mcbronkowitch/fireflow/docs/hardware/captures/README.md

# Raw board captures — 2026-09-18/19 codec-tone campaign, 2026-09-28 pot round and scan check

Serial output from the Daisy Patch Submodule, as captured. Unedited.

These are here because committed files cite them **as the provenance of
numbers that ship**, and a citation pointing into deletable scratch is not a
citation:

| capture | what depends on it |
|---|---|
| `task-3-board-capture-1c15987.txt` | boot 1 of the four-boot boot-virgin floor |
| `task-4-board-capture-438fd51.txt` | boot 2 of the same |
| `task-4-board-capture-c5631f4.txt` | boot 3 of the same |
| `task-5-board-capture.txt` | boot 4, plus the whole window sweep |
| `task-6-board-capture-silent-arm.txt` | boot 5 — the silent-cadence arm, which answers section 6 |
| `pot-settle-capture-618427c.txt` | `shell/test_read_settle.py` (the real-block section) and the round-four write-up `docs/hardware/pots-measured.md` |
| `pot-wait-capture-e20b8fd.txt` | `shell/test_read_wait.py` (the real-block section) and the round-four write-up `docs/hardware/pots-measured.md` |
| `scan-check-capture-c04ba77.txt` | `shell/test_read_scan_check.py` (the capture section), the write-up `docs/hardware/scan-measured.md`, and `kPotHysteresis` in `shell/scan_value.h` |

The four-boot floor is `BOOT_VIRGIN_FLOOR` in `../../../shell/read_tone.py`,
which gate G8(b) compares against, and the same four columns appear in the
codec-tone design spec's section 7. Each figure is the `settled_mean_spread`
field of the `SHELL_TONE_STAT` lines at `case=-1` through `case=-5` — the
negative case numbers are the per-victim boot-virgin rows, emitted once per
boot before any `StartAudio()` and re-emitted verbatim every block.

`task-5-board-capture.txt` opens mid-block and closes mid-block; **lines 898
to 1852 are the one complete block**, and that block is also vendored as
`../../../shell/testdata/tone-block-86070d9.txt`, which the reader's guard
parses on every `ctest` run.

`task-6-board-capture-silent-arm.txt` is the run that answered
`../codec-tone-measured.md` section 6: the image `ab02aec+` carries the
silent-cadence arm (`level=3` on `SHELL_TONE_CASE`), so each block holds a
tone measurement and a no-tone measurement **at the same cadence**. It too
opens mid-block: **lines 1192 to 2401 are the one complete block**, and every
figure in that section comes from it. It carries **no `$$` overflow marker at
all** in 2925 lines, which is worth recording because the arm added 255 lines
to a block — those lines print slowly, one per phase point across a 10 ms
wait, so the extra volume never pressed on the host's drain rate. The reader's
guard parses this file on every `ctest` run as well.

This capture is one boot, three blocks. The two complete ones agree: across
their thirty tone-versus-silent rows no difference exceeds one count.

The round-one crosstalk capture of 2026-09-19 is **not** here: at 2 MB it is
an order of magnitude larger than these five, and its first complete block is
already committed in derived form as `../2026-09-19-xtalk.csv` and
`../2026-09-19-xtalk.csv.meta.csv`. Its `g6=0` readings across ten blocks are
recorded in `../crosstalk-measured.md` and exist in raw form only in the
session workspace.

`pot-settle-capture-618427c.txt` is the settle probe's pot-round image
(`SHELL_COUPON_PROBE=1 SHELL_SETTLE_PROBE=1 SHELL_POT_ROUND=1`), captured
2026-09-28 on the one coupon board with RV2, RV4 and RV6 set to mid travel. It
holds three complete blocks; the file opens mid-block, on a partial block
that started before the port opened, and the first complete block starts at
line 708.

`pot-wait-capture-e20b8fd.txt` is the wait probe's pot-round image
(`SHELL_COUPON_PROBE=1 SHELL_WAIT_PROBE=1 SHELL_POT_ROUND=1`), captured the
same day on the same board with the same pot settings. It too holds three
complete blocks after an opening partial one; the first complete block starts
at line 412.

`scan-check-capture-c04ba77.txt` is the panel scan's measurement image
(`SHELL_COUPON_PROBE=1 SHELL_SCAN_CHECK=1`), captured 2026-09-28 on the same
board, RV2, RV4 and RV6 still at mid travel from the pot round, the engine
playing and the codec running. It holds five complete run blocks; lines 1–75
are a partial opening (line 2 carries a `$$` marker), and the first complete
block starts at line 76. The guard also compares `kPotHysteresis` with the H
it computes from this file, so replacing the capture moves the constant.

A capture is evidence, not a document. Nothing here is edited to read better,
and where a capture contradicts a write-up, the capture wins.
