mcbronkowitch/fireflow/docs/hardware/io-budget.md

# I/O-Budget — FireFlow auf 60 HP

> **Stand 2026-08-30.** Ursprünglich am 2026-08-08 (Git `9326fee`) als
> **Vorarbeit auf 42 HP** geschrieben, mit leerer Einstufungsspalte in §2, weil
> die Panel-Reduktion Instrumentendesign ist und Bastian gehört.
>
> **Diese Prämisse ist zweimal überholt worden, und beide Male nach oben.** Die
> Envelope-Entscheidung (`2026-08-08-fireflow-hardware-envelope-design.md`)
> setzte 60 HP mit vollem Control-Set, und die Bedienelement-Reduktion
> (`2026-08-09-hw-control-reduction-design.md`) senkte das Inventar von 82 auf
> 68 Parameter. Danach haben **drei Panel-Runden** — Neugruppierung (2.21.1),
> Neuverteilung (2.21.2) und Plattenrunde 2a (2.21.3) — Controls verschoben,
> zusammengelegt und die Bauform geändert.
>
> **Nachtrag 2026-08-19.** Zwei Zahlen korrigiert, beide gefunden, indem der
> Generator gelaufen ist statt zitiert zu werden — der Fehler, vor dem §1
> warnt: die 595-Bilanz rechnete mit den **21** LEDs des Rack-Panels statt den
> **19** der Hardwareplatte (§3, §4), und die CPU-Reserve stand als
> Seed-Hochrechnung (2,17 Punkte) statt als die inzwischen direkt gemessenen
> ~2,9 (§6). Beide Korrekturen gehen zugunsten des Entwurfs aus.
>
> **Nachtrag 2026-08-30. §1, §2 und §4 neu gemessen, und es hatte sich wieder
> bewegt.**
> Zwischen dem 19. und dem 30. August sind die MOD-Latch-Runde
> (`2026-08-22-mod-latch-layer-design.md`) und PAN (`2026-08-30-pan`) gelandet;
> §1 stand danach elf Tage falsch da. Es waren keine Rundungsfehler, sondern das
> Inventar: 69 → **75** Parameter auf der Platte, 67 → **73** Positionen, die
> Bauformverteilung 16/51/2 → **14/58/3**, `HW_ONLY` 2 → **1** (`MODBTN` ist ein
> echter `ParamId` geworden), und die Kernaussage „keine hardware-only
> Parameter" musste ihre Prüfmenge wechseln (`PARAMS`, nicht
> `RUNTIME_PANEL_PARAMS`). Der Grund, dass es niemandem auffiel: der Wächter
> `tools/test_count_panel_controls.py` stand seit dem 7. August rot und wurde
> gelesen wie Rauschen. Er ist am 2026-08-30 neu geeicht, mit der Anweisung, §1
> im selben Commit mitzuziehen.
>
> **§2 und §4 sind am selben Tag mitgezogen worden.** §2 trug eine
> 69-Zeilen-Tabelle; die Platte hat 75. Sie ist neu **erzeugt** statt
> nachgepflegt — und dabei kam heraus, dass nicht nur sechs Zeilen fehlten:
> **25 der alten 69 hatten auch ihre Position oder ihre Bauform geändert**
> (`REV_MIX_A/B` ist gar kein grosser Poti mehr). §4 nannte „67
> Poti-/Taster-Positionen, 2 reservierte Pads"; es sind **73** und **1**, und
> die Geometriezeile hatte eine Reihe (76 → 74,4) und beide waagerechten Ränder
> falsch. Die 19 LEDs, 18 Buchsen und der SD-Slot stimmten durchweg.
>
> **Was das für dieses Dokument heißt:** §1, §2 und §4 sind auf das **gebaute**
> Panel nachgezogen und am 2026-08-30 gemessen. §5 (Buchsen, 12/6) gilt
> unverändert weiter, am selben Tag gegengeprüft. §3 (Pins) ist von der
> Parameterzahl unabhängig und steht unverändert; es hat nur einen Nachtrag zur
> Mux-Topologie bekommen. §6 listet, was heute noch offen ist — es ist eine
> andere Liste als 2026-08-08.
>
> **Stand 2026-10-08: welche Teile noch die Platte vor dem 9-mm-Raster
> beschreiben.** Die 9-mm-Korrektur (Spec `2026-10-07-panel-nine-mm-raster-design.md`)
> hat jedes Bedienelement neu gesetzt. Gemessen am 2026-10-09:
> `python res/gen_hw_panel.py` druckt `params=75 inputs=12 outputs=6 lights=15
> panel=60HP`. Die folgenden Stellen sind **nicht** nachgezogen; sie stehen auf
> dem Stand 2026-08-30 und werden mit diesen Zahlen gelesen:
>
> - **§1, Codeblock (`lights=19`):** heute `lights=15`. Die Bauformtabelle zählt
>   Parameter-Positionen nach `HW_PARAMS` (14 / 56 / 3); mit `HW_ONLY` sind es
>   **77 Positionen**: 14 grosse Potis, 59 kleine (darunter drei reservierte), 4
>   Taster. Das sind 73 Potis und 4 Taster.
> - **§1, „1 Element … `HW_ONLY`“:** heute **4**: `SHIFTBTN` (Taster) und die
>   drei reservierten Potis `ROOT_A`, `ROOT_B`, `REV_MOD` (Beschriftung ROOT
>   und WOBL), die einen Mux-Kanal lesen, aber nichts schicken. Die Zahl der
>   Taster bleibt 4.
> - **§1, Körperradien „6,0 / 4,4 / 4,0 mm“:** heute `BODY_R` = **6,0 / 3,85 /
>   3,0 mm** (gross / klein / Taster); `CLASS_R` ist unverändert 8,5 / 6,0 /
>   4,0 mm.
> - **§3, 595-Zeile (19 LEDs, 5 Enables):** heute 15 LEDs, und die Kette ist
>   40 Bit lang: Adresse Bit 0–2, Enables Bit 3–12 (zehn, eins je Mux), LEDs
>   Bit 13–27 (`shell/generated_panel_map.h`). Die Mux-Zeile steht im Nachtrag
>   2026-10-08 in §3.
> - **§4, „neun Linien“, y = 114 mm, 19 LEDs, 1 reserviertes Pad:** heute
>   **fünf Reihen** bei y = 14,5 / 34,625 / 54,75 / 74,875 / 95,0 mm (Raster
>   20,125 mm), die Buchsenreihe bei **y = 112,75 mm** (`JACK_Y`), die
>   Bedienelemente von x = 11,0 bis x = 293,8 mm, **15 LEDs**, und
>   `SHIFTBTN` ist das eine reservierte Pad (daneben die drei reservierten
>   Potis). Plattenmaß 304,8 × 128,5 mm unverändert.

## 1. Die Ausgangslage

**Autorität ist der Generator, nicht dieses Dokument.** Eine Handzählung
veraltet beim nächsten Panel-Commit; jede Zahl unten stammt aus einem Lauf und
ist mit ihm reproduzierbar.

```
python host/vcv/res/gen_hw_panel.py          # aus host/vcv/, idempotent
params=75 inputs=12 outputs=6 lights=19  panel=60HP

python tools/count_panel_controls.py         # aus dem Repo-Wurzelverzeichnis
panel 68 · appended 6 · runtime 74 · part_a 20 · part_b 20 · shared 10
```

Beide Zahlen sind gemessen 2026-08-30. **Sie sind nicht mehr dieselbe Zahl, und
das ist kein Fehler:** die Platte trägt 75 Parameter, `RUNTIME_PANEL_PARAMS`
hat 74. Der eine Unterschied ist `MODBTN`. Er ist trotzdem **kein**
hardware-only *Parameter* — er ist ein echter `ParamId`, er kommt nur aus einem
anderen Block: `MOD_LAYER_PARAMS` (51 ids, Spec
`2026-08-22-mod-latch-layer-design.md`), nicht aus der Panel-Liste. Zusammen
sind das `gen_panel.PARAMS` = 74 + 51 = **125**, und *gegen die* ist die
Differenzmenge leer: kein Element der Hardwareplatte ist ein Parameter, den
VCV nicht auch hat.

> **Die alte Formulierung prüfte gegen `RUNTIME_PANEL_PARAMS` und stimmt seit
> der MOD-Latch-Runde nicht mehr.** Wer die Aussage nachprüft, muss gegen
> `gen_panel.PARAMS` prüfen, sonst fällt `MODBTN` fälschlich als
> hardware-only heraus.

Was auf der Hardware existiert und **gar keinen** Parameterwert hat, sind die
LEDs und ein einziger Taster — siehe unten.

**75 Parameter auf 73 physischen Positionen.** Die Differenz sind die beiden
bewussten Doppelbelegungen: `STAGES_A/B` (BEND) teilt sich den Knopf mit
`ATTACK_A/B` (68,25 / 34,00 und 236,55 / 34,00), mit engine-abhängigem
Moduswechsel. Das ist die einzige Mehrfachbelegung auf dem Panel.

Nach Bauform **auf der Hardware** — nicht nach dem VCV-Glyph, der eine andere
Größenklasse haben darf und bei mehreren Controls auch hat:

| Bauform | Radius | Anzahl | Positionen |
|---|---:|---:|---:|
| grosser Poti (`G`) | 8,5 mm | 14 | 14 |
| kleiner Poti (`S`) | 6,0 mm | 58 | 56 |
| Taster (`P`) | 4,0 mm | 3 | 3 |
| **Summe** | | **75** | **73** |

Die Radiusspalte ist `CLASS_R` — der Abstandsradius, mit dem das Layout rechnet,
nicht der Körper. Die Körperradien (`BODY_R`) sind 6,0 / 4,4 / 4,0 mm.

Dazu **1** Element, das gar keinen `ParamId` hat und deshalb in keiner der
Zahlen oben steckt (`HW_ONLY` im Generator):

| Element | Art | Anmerkung |
|---|---|---|
| `SHIFTBTN` | Taster | reserviert, ohne Funktion — 1 weiteres Pad |

Macht **4 Taster**: `REC_A/B`, `MODBTN` (seit der MOD-Latch-Runde ein echter
Parameter, kein `HW_ONLY` mehr — deshalb steht er jetzt in der `P`-Zeile oben)
und das reservierte `SHIFTBTN`.

**Die LEDs laufen seit der LED-Feedback-Runde (2026-08-16) nicht mehr über
`HW_ONLY`.** Alle Lampen auf der Platte sind jetzt echte `LightId`s.

> **Drei verschiedene LED-Zahlen, und dieser Abschnitt hat sie bis 2026-08-19
> vermischt.** Sie sind alle drei richtig, nur für verschiedene Dinge:
>
> | Zahl | Was sie zählt | Woher |
> |---:|---|---|
> | **17** | `LightId`s insgesamt, alle jeden Block geschrieben | `gen_panel.LIGHTS` (4) + `HW_ONLY_LIGHTS` (13) |
> | **15** | Lampen auf der **Hardwareplatte** | `gen_hw_panel.py` druckt `lights=15` |
> | **4** | Lampen auf dem **Rack**-Panel | `count_panel_controls.py` druckt `lights 4` |
>
> Die 15 sind die 17 ohne `FLOW_A_L`/`FLOW_B_L`, die `_SKIP_HW_LIGHTS` auf der
> Hardwareplatte bewusst weglässt. **Für die 595-Kette zählen die 15** — sie
> trägt physische Lampen, keine `LightId`s (§3). *Stand 2026-10-08: die
> 9-mm-Korrektur (Spec 2026-10-07 §5) hat die Platte von 19 auf 15 Lampen
> gebracht; die Zahlen 21 und 19 stammten aus der Zeit davor.*

Der Bestand: 8 der bisherigen 10 blieben, `CAP_A_L`/`CAP_B_L` sind mit der
Capture-Sequenz gelöscht (die gibt es seit 2026-07-14 nicht mehr, siehe
`docs/roadmap.md`), und 13 sind neu *(Stand 2026-08-19; 8 + 13 sind 21, die Zahl
des Rack-Panels jener Zeit, nicht die 17 `LightId`s und 15 Plattenlampen des
Kastens oben)*. *(Stand 2026-10-08, 15 Lampen auf der
Platte, Spec 2026-10-07 §5: `SYNC_L` heißt jetzt `CLK_L` und soll jeden Impuls
an der CLOCK-Buchse blitzen; neu sind `RST_L`, `FTIME_A_L`/`FTIME_B_L`. Die
zwei Pad-Lampen `SHIFTBTN_L` und `MODBTN_L` stehen zwischen ihrer Taste und
ihrer Buchse und **tragen je zwei Aufgaben**: `SHIFTBTN_L` zeigt gerastetes
SHIFT, sonst den Eingangspegel; `MODBTN_L` zeigt MODs Doppelpuls, sonst den
Master-Limiter, den vorher `CEIL_L` zeigte, das damit entfällt.)* Von diesen
ist heute im Code nur `MODBTN_L` belegt; `CLK_L`, `RST_L`, `FTIME_*_L` und `SHIFTBTN_L`
sind vorerst dunkel — ihre Bedeutung ist P6b (`led_law.hpp`, `fill()`) —, aber
jeden Block *geschrieben*, nicht übersprungen; ein Gate prüft das. Das
gilt auch für `FLOW_A_L`/`FLOW_B_L`, die geschrieben werden, obwohl die
Hardwareplatte sie nicht zeichnet. `TEMPO_L` tickt den Transport-Beat
(Metronom-Puls, `kTempoPulse` der Beat-Phase). Herleitung, Platzierung und die offene
Mux-Breite (8:1 gegen 16:1, deshalb nimmt `duty()` den Schrittzähler als
Parameter): Spec
[`2026-08-16-led-feedback-design.md`](../superpowers/specs/2026-08-16-led-feedback-design.md)
§2–§3, und `docs/roadmap.md`.

> **Die LED-Zahl war erst gefallen, und zwar absichtlich.** Die Neugruppierung
> hatte das Feld auf 20 festgelegt (Envelope-Spec §1, oberes Ende des
> Korridors); die Neuverteilung hat `ENGINE_A/B` vom Taster zum
> **fünf-Zonen-Rastpoti** am Kopf der VOICE-Gruppe gemacht und damit zehn
> Anzeige-LEDs eingespart. 20 − 10 = 10, und die Kette blieb dieselbe — bis
> die LED-Feedback-Runde das Feld auf 21 `LightId`s anhob (19 davon auf der
> Platte, siehe Kasten oben), mehr als das ursprüngliche Korridor-Ende, weil
> kein Rundungsdruck mehr bestand.

`HIDDEN_PARAMS` ist seit der Reduktionsrunde leer — es gibt keinen menü-only
*Parameter* mehr. Das Kontextmenü selbst existiert weiter (Resync to bar, BBD
Freeze Attack, die Sampler-Untermenüs, Excitation-Flags), es trägt nur keinen
Wert mehr, der nicht auch auf dem Panel sitzt.

## 2. Die 75 Parameter

Die Einstufungsspalte dieses Abschnitts war bis 2026-08-09 leer und war die
offene Frage des ganzen Dokuments. **Sie ist entschieden.** Was hier steht, ist
nicht mehr eine Absicht, sondern das gebaute Panel, ausgelesen aus
`host/vcv/res/gen_hw_panel.py` (`HW_PARAMS`, `hw_class()`, Positionen in mm vom
linken oberen Panelrand). Die Prüfsumme der Zeilen ist **75**.

**Die Tabelle ist generiert, nicht gepflegt** (Neustand 2026-08-30). Reihenfolge
und Nummerierung sind die von `HW_PARAMS`, die Bauform kommt aus `hw_class()`,
die Gruppe aus `PART_A`/`PART_B`/`SHARED` — alles andere bekommt „—". Wer sie
neu erzeugt, prüft die Herleitung daran, dass die unveränderten Zeilen Zeichen
für Zeichen zurückkommen.

> **Sie stand länger falsch da, als die sechs fehlenden Zeilen vermuten
> lassen.** Beim Neuerzeugen kamen nicht nur die neuen Parameter dazu: **25 der
> alten 69 Zeilen hatten sich bewegt** (gemessen, nicht geschätzt — die
> übrigen 44 kamen unverändert zurück). `ENGINE_A/B` sitzt jetzt in der oberen
> Außenecke (16,25 bzw. 288,55 / 14,50) statt bei y = 50,22. **Die Reihe
> y = 76 gibt es nicht mehr:** sie ist auf 74,4 (TUNE, DETUNE, REV_SIZE,
> REV_DIFF) und 79 (FLUX, COMP) aufgeteilt. Von y = 95 sind einzelne Elemente
> auf 97 gerückt (GRIT, FLUXFB, REV_MIX) — die Reihe 95 selbst gibt es weiter,
> `COLOR_A/B` steht unverändert darauf. `SOURCE_A/B` und `FILT_A/B` sind
> waagerecht gerückt, und `REV_MIX_A/B` ist vom **grossen** auf den **kleinen**
> Poti gewechselt. Welche der Runden das jeweils war, steht hier bewusst nicht
> — es wurde nicht nachgeschlagen. Eine Position aus der alten Tabelle zu
> zitieren, hätte ein Bohrbild ruiniert.

| # | Parameter | Bauform auf der Hardware | Gruppe | Position (mm) |
|---:|---|---|---|---|
| 1 | `RATE_A` | kleiner Poti | PART_A | 61,00 / 14,50 |
| 2 | `SHAPE_A` | kleiner Poti | PART_A | 18,25 / 34,00 |
| 3 | `DENSITY_A` | grosser Poti | PART_A | 40,75 / 53,00 |
| 4 | `SMOOTH_A` | kleiner Poti | PART_A | 31,25 / 34,00 |
| 5 | `RANGE_A` | kleiner Poti | PART_A | 44,25 / 34,00 |
| 6 | `MELODY_A` | kleiner Poti | PART_A | 74,00 / 14,50 |
| 7 | `MOD_A` | grosser Poti | PART_A | 21,75 / 53,00 |
| 8 | `TUNE_A` | kleiner Poti | PART_A | 17,00 / 74,40 |
| 9 | `ATTACK_A` | kleiner Poti | PART_A | 68,25 / 34,00 — geteilt mit `STAGES_A` |
| 10 | `DECAY_A` | kleiner Poti | PART_A | 81,25 / 34,00 |
| 11 | `RES_A` | kleiner Poti | PART_A | 94,25 / 34,00 |
| 12 | `SUB_A` | kleiner Poti | PART_A | 107,25 / 34,00 |
| 13 | `SOURCE_A` | kleiner Poti | PART_A | 72,88 / 50,22 |
| 14 | `FLUX_A` | grosser Poti | PART_A | 67,00 / 79,00 |
| 15 | `GRIT_A` | kleiner Poti | PART_A | 116,75 / 97,00 |
| 16 | `COMP_A` | grosser Poti | PART_A | 106,50 / 79,00 |
| 17 | `STEPS_A` | kleiner Poti | PART_A | 35,00 / 14,50 |
| 18 | `ENGINE_A` | kleiner Poti | PART_A | 16,25 / 14,50 |
| 19 | `DETUNE_A` | kleiner Poti | PART_A | 30,00 / 74,40 |
| 20 | `SONG_A` | kleiner Poti | PART_A | 48,00 / 14,50 |
| 21 | `RATE_B` | kleiner Poti | PART_B | 243,80 / 14,50 |
| 22 | `SHAPE_B` | kleiner Poti | PART_B | 286,55 / 34,00 |
| 23 | `DENSITY_B` | grosser Poti | PART_B | 264,05 / 53,00 |
| 24 | `SMOOTH_B` | kleiner Poti | PART_B | 273,55 / 34,00 |
| 25 | `RANGE_B` | kleiner Poti | PART_B | 260,55 / 34,00 |
| 26 | `MELODY_B` | kleiner Poti | PART_B | 230,80 / 14,50 |
| 27 | `MOD_B` | grosser Poti | PART_B | 283,05 / 53,00 |
| 28 | `TUNE_B` | kleiner Poti | PART_B | 287,80 / 74,40 |
| 29 | `ATTACK_B` | kleiner Poti | PART_B | 236,55 / 34,00 — geteilt mit `STAGES_B` |
| 30 | `DECAY_B` | kleiner Poti | PART_B | 223,55 / 34,00 |
| 31 | `RES_B` | kleiner Poti | PART_B | 210,55 / 34,00 |
| 32 | `SUB_B` | kleiner Poti | PART_B | 197,55 / 34,00 |
| 33 | `SOURCE_B` | kleiner Poti | PART_B | 231,93 / 50,22 |
| 34 | `FLUX_B` | grosser Poti | PART_B | 237,80 / 79,00 |
| 35 | `GRIT_B` | kleiner Poti | PART_B | 188,05 / 97,00 |
| 36 | `COMP_B` | grosser Poti | PART_B | 198,30 / 79,00 |
| 37 | `STEPS_B` | kleiner Poti | PART_B | 269,80 / 14,50 |
| 38 | `ENGINE_B` | kleiner Poti | PART_B | 288,55 / 14,50 |
| 39 | `DETUNE_B` | kleiner Poti | PART_B | 274,80 / 74,40 |
| 40 | `SONG_B` | kleiner Poti | PART_B | 256,80 / 14,50 |
| 41 | `MORPH` | grosser Poti | SHARED | 152,40 / 53,00 |
| 42 | `TEMPO` | kleiner Poti | SHARED | 139,40 / 34,00 |
| 43 | `COUPLE` | kleiner Poti | SHARED | 152,40 / 34,00 |
| 44 | `SCALE` | kleiner Poti | SHARED | 132,90 / 14,50 |
| 45 | `DRIFT` | kleiner Poti | SHARED | 145,90 / 14,50 |
| 46 | `REV_SIZE` | kleiner Poti | SHARED | 136,40 / 74,40 |
| 47 | `REV_DECAY` | grosser Poti | SHARED | 152,40 / 79,00 |
| 48 | `REV_TONE` | kleiner Poti | SHARED | 152,40 / 97,00 |
| 49 | `REV_DIFF` | kleiner Poti | SHARED | 168,40 / 74,40 |
| 50 | `CHOKE` | kleiner Poti | SHARED | 158,90 / 14,50 |
| 51 | `FILT_A` | grosser Poti | — | 88,88 / 53,00 |
| 52 | `FILT_B` | grosser Poti | — | 215,93 / 53,00 |
| 53 | `TIDE` | kleiner Poti | — | 136,40 / 50,22 |
| 54 | `FLUXRATE_A` | kleiner Poti | — | 54,00 / 89,86 |
| 55 | `FLUXRATE_B` | kleiner Poti | — | 250,80 / 89,86 |
| 56 | `FLUXFB_A` | kleiner Poti | — | 67,00 / 97,00 |
| 57 | `FLUXFB_B` | kleiner Poti | — | 237,80 / 97,00 |
| 58 | `COLOR_A` | grosser Poti | — | 23,50 / 95,00 |
| 59 | `COLOR_B` | grosser Poti | — | 281,30 / 95,00 |
| 60 | `LINK_A` | kleiner Poti | — | 80,00 / 89,86 |
| 61 | `LINK_B` | kleiner Poti | — | 224,80 / 89,86 |
| 62 | `STAGES_A` | kleiner Poti | — | 68,25 / 34,00 — geteilt mit `ATTACK_A` |
| 63 | `STAGES_B` | kleiner Poti | — | 236,55 / 34,00 — geteilt mit `ATTACK_B` |
| 64 | `REC_A` | Taster | — | 101,00 / 14,50 |
| 65 | `REC_B` | Taster | — | 203,80 / 14,50 |
| 66 | `REV_MIX_A` | kleiner Poti | — | 129,75 / 97,00 |
| 67 | `REV_MIX_B` | kleiner Poti | — | 175,05 / 97,00 |
| 68 | `SHUFFLE` | kleiner Poti | — | 165,40 / 34,00 |
| 69 | `PACE` | kleiner Poti | — | 168,40 / 50,22 |
| 70 | `DEPTH_A` | kleiner Poti | — | 104,88 / 50,22 |
| 71 | `DEPTH_B` | kleiner Poti | — | 199,93 / 50,22 |
| 72 | `PULL` | kleiner Poti | — | 171,90 / 14,50 |
| 73 | `PAN_A` | kleiner Poti | — | 103,75 / 97,00 |
| 74 | `PAN_B` | kleiner Poti | — | 201,05 / 97,00 |
| 75 | `MODBTN` | Taster | — | 290,80 / 114,00 |

**Zugegangen seit der Reduktion** — sechs Zeilen, und keine davon hat etwas
verdrängt. Das ist der eigentliche Beleg dafür, dass „one in, one out" tot ist:

| Zeile | Parameter | Woher |
|---:|---|---|
| 69 | `PACE` | globaler Modulations-Zeitdehner, Spec 2026-08-12 modulation-pace |
| 70–71 | `DEPTH_A/B` (DPTH) | die `LANE_MOTION`-Basis, aus FEED gewachsen — Spec 2026-08-18 feed §4, auf alle sechs Engines gezogen in 2026-08-19 voice-knobs-dpth-edge |
| 72 | `PULL` | bipolare Akkord-Schwerkraft zwischen den Decks, Spec 2026-07-19 pull-chord-gravity |
| 73–74 | `PAN_A/B` | Deck-Balance im Master-Mix, Spec 2026-08-30 pan — auf `LEVEL_SLOTS[0]`, den die Platte dafür freigehalten hatte |
| 75 | `MODBTN` | **kein neues Bedienelement.** Das Pad gab es schon, es lief bis zur MOD-Latch-Runde (Spec 2026-08-22) als `HW_ONLY` ohne Parameterwert — jetzt ist es ein echter `ParamId` und zählt mit (§1) |

**Der Satz, der hier bis 2026-08-30 stand** — `PACE` sei „der einzige
Parameter, den das Instrument seit der Reduktion dazubekommen hat" — wurde mit
`d18e50f` (2026-08-19, DPTH) falsch und ist es elf Tage lang geblieben;
`ee23912` (08-22, PULL) und `32835ff` (08-30, PAN) sind danach darüber
hinweggelaufen.

**Retiriert und nicht mehr Teil der Zählung** (Begründung in
`2026-08-09-hw-control-reduction-design.md`): `GRITMODE_A/B`, `STEP_A/B`,
`FORM_A/B`, `NEWPHRASE_A/B`; `SYNC`, `SPOT`, `MASTER_DRIVE`, `SETTLE`,
`REV_SMEAR`, `REV_MOD`; `FLUXTIME_A/B` (in FLUX aufgegangen); `DRIVE_A/B`
(ersatzlos, BBD-Drive kommt aus `bbd_engine.cpp`).

**Dazugekommen und wieder weg, ohne je in dieser Tabelle gestanden zu haben:**
`DAMP_A/B` (der EDGE-Knopf, ROW_V2 unter DPTH) kam am 2026-08-19 mit DPTH und
ging am 2026-08-20 wieder (Plan `edge-knob-removal`) — gemessen und verworfen,
er hat seinen Panelplatz nicht verdient. Der Platz bleibt absichtlich leer;
freigewordene Slots werden nicht neu gruppiert.

**Eine offene Kleinigkeit, die genau hier auffällt:** `STAGES` hat im Generator
ein **leeres Plattenwort** (`HW_CAPTION["STAGES"] = ""`), BEND wird also gar
nicht aufs Panel gedruckt. Das ist bekannt und nicht entschieden — auf der
Hardware ist der Knopf da, die Beschriftung nicht.

## 3. Was das Patch Submodule wirklich hergibt

Gelesen aus `lib/libDaisy/src/daisy_patch_sm.h` (Pinliste) und
`daisy_patch_sm.cpp:10-21` (ADC-Zuordnung). **Das ist der Teil dieses
Dokuments, der die Reduktion am härtesten einschränkt** — und der einzige, den
die drei Panel-Runden nicht berührt haben.

Das Modul hat 40 Anschlüsse (A1–A10, B1–B10, C1–C10, D1–D10). Davon sind
vergeben und nicht verfügbar:

| Pins | Belegung |
|---|---|
| A1, A4, A5, A6, A7, A10 | −12 V, GND, +12 V, +5 V, GND, +3V3 |
| A8, A9 | USB D−/D+ — **wird für DFU gebraucht**, das Board hat keine SWD-Pins |
| B1–B4 | Audio Out R/L, Audio In R/L |

Bleibt für Bedienelemente und Buchsen:

| Pins | Funktion | brauchbar als |
|---|---|---|
| C2–C9 | CV In 1–8 | 8 ADC-Eingänge **mit bipolarer Eingangsstufe** (±5 V → 0–3,3 V) |
| **A2, A3** | UART1 Rx/Tx | **ADC 9/10 — rohe 0–3,3-V-Eingänge** |
| **D8, D9** | SPI2 MISO/MOSI | **ADC 11/12 — rohe 0–3,3-V-Eingänge** |
| C1, C10 | CV Out 1/2 | 2 DAC-Ausgänge, **0–5 V unipolar** |
| B5, B6 | Gate Out 1/2 | 2 digitale Ausgänge |
| B9, B10 | Gate In 1/2 | 2 digitale Eingänge |
| B7, B8 | I2C1 SCL/SDA | I2C oder 2 GPIO |
| D1, D10 | SPI2 CS/SCK | SPI oder 2 GPIO |
| D2–D7 | SDMMC | SD-Karte oder 6 GPIO |

### Die entscheidende Zahl: vier rohe ADC-Pins

Ein Poti liefert 0–3,3 V. Dafür taugen **A2, A3, D8, D9** — die acht CV-Pins
tragen die bipolare Eingangsstufe des Moduls und würden ein unipolares
Potisignal auf einen Teil des ADC-Bereichs stauchen.

> **Nachtrag 2026-08-08 (Envelope-Spec §2), und er ändert das Ergebnis:** die
> Rechnung unten geht davon aus, dass die Adressleitungen GPIOs kosten. Das tun
> sie nicht mehr — **Adress- *und* Enable-Leitungen der 74HC4067 wandern auf die
> 595-Kette.** Damit teilen sich bis zu **acht** Muxe die vier Sense-Pins:
> **128 Kanäle für null GPIOs.** Genau diese Einsparung ist es, die den
> 4-bit-SD-Anschluss überhaupt möglich macht. Bedarf heute: **67 Positionen** —
> die Mux-Kapazität ist damit nicht mehr die knappe Ressource, die sie 2026-08-08
> war.

```
Mux-Kanäle = rohe ADC-Pins × Kanäle pro Chip

  4 × 74HC4051  (8:1)  = 32 Kanäle,  3 Adress-GPIO (geteilt)
  4 × CD74HC4067 (16:1) = 64 Kanäle, 4 Adress-GPIO (geteilt)
  8 × CD74HC4067 (16:1) = 128 Kanäle, 0 GPIO (Adressen über die 595-Kette)
```

`InitMux()` in `lib/libDaisy/src/per/adc.h` treibt die Adressleitungen selbst
und scannt per DMA. Der Mux-Scan kostet damit in der Audioschleife praktisch
nichts — die Warnung im Plan vor blockierendem Scan gilt `src/hw/sr_165.h`,
dem Schieberegister für Taster, nicht dem analogen Mux.

### libDaisy kann diesen Mux-Entwurf nicht — das ist ungeplante Firmware-Arbeit

Zwei Befunde, beide aus der Bibliothek gelesen (2026-08-16), und der zweite ist
der teure.

**Erstens: die Stock-Init belegt alle zwölf Kanäle.** `DaisyPatchSM::Init()`
legt sie mit `InitSingle` an (`daisy_patch_sm.cpp:318-322`) und konditioniert
die ersten acht mit `InitBipolarCv`, die vier rohen mit dem einfachen `Init`
(`:324-331`). `InitSingle` und `InitMux` schließen sich pro Kanal aus — die
Mux-Kette auf ADC_9..12 bekommt man also nicht dazu, indem man die Stock-Init
laufen lässt und danach ergänzt.

**Zweitens, und das wiegt schwerer: `InitMux` kann nur 8:1, und nur an GPIOs.**
`AdcChannelConfig::InitMux` nimmt drei Adresspins (`MUX_SEL_LAST == 3`,
`adc.h:34-40`) und klemmt die Kanalzahl hart:
`mux_channels_ = mux_channels < 8 ? mux_channels : 8` (`adc.cpp:183`). Die
Adressleitungen werden als `GPIO::Mode::OUTPUT` initialisiert und von libDaisy
selbst getrieben (`adc.cpp:185-191`). **Der Entwurf dieses Dokuments ist damit
mit der Bibliothek, wie sie ist, nicht baubar:**

- 4 Sense-Pins × 8 Kanäle = **32 Kanäle gegen 65 Bedarf** — Faktor zwei zu wenig.
- Die drei Adress-GPIOs müssten aus dem Pool kommen, und der ist nach dem
  SD-Slot leer (GPIO-Bilanz unten).

Was daraus folgt, ist keine Absage an die Topologie — die ist elektrisch
richtig und der Grund, warum der SD-Slot überhaupt passt. Es folgt daraus, dass
**der ADC-Scan für 16:1 mit Adressen aus der 595-Kette selbst geschrieben
werden muss**. Der DMA-Scan der `AdcHandle` bleibt nutzbar; was fehlt, ist die
Kanalumschaltung. Diese Arbeit ist in keiner Spec und in keinem Plan
veranschlagt und gehört ins Bring-up (M6, Schritt 2).

**Die acht CV-Kanäle sind von beidem nicht betroffen** und bleiben, wie
libDaisy sie liefert.

### Kollision, die man kennen muss: SPI2 gegen ADC 11/12

**`D8`/`D9` sind gleichzeitig SPI2 MISO/MOSI und ADC 11/12.** Wer den SPI-Bus
benutzt — etwa für einen `MAX11300` —, verliert damit **die Hälfte der rohen
ADC-Pins** und kommt auf die halbe Mux-Kapazität. Das ist keine Kleinigkeit,
sondern genau die Stelle, an der sich die zwei I/O-Strategien gegenseitig im
Weg stehen. Die Envelope-Spec hat daraus eine Regel gemacht: **SPI2 ist tabu**,
solange nichts Zwingendes auftaucht.

### Die GPIO-Bilanz, vollständig

Pool: B7, B8, D1, D10, D2–D7 = **10**.

| Verbraucher | Pins |
|---|---:|
| SDMMC 4-bit (D2–D7) — Pflicht, siehe §5 | 6 |
| 595/165-Ketten, gebitbangt (Daten-Out, Takt, Latch/Load, Daten-In) | 4 |
| **Rest** | **0** |

**Die Pin-Reserve ist null, und das ist Absicht:** die Reserve steckt in den
Ketten, nicht in den Pins. Jede Erweiterung — mehr LEDs, mehr Taster, mehr Muxe
— kostet ein weiteres Schieberegister an der vorhandenen Kette und **keinen**
GPIO. Die 20-%-Reserve-Regel des Phase-0-Plans gilt hier auf Ketten-Ebene.

**Die Reihenfolge ist wichtig, weil sie oft rückwärts erzählt wird:** der
SD-Slot wurde nicht dazugenommen und dann gehofft, dass es reicht. Die
Adressleitungen sind auf die 595-Kette gewandert, **damit** die sechs
SDMMC-Pins frei bleiben. Hätten die Muxe ihre Adressen an GPIOs, gäbe es
keinen 4-bit-SD-Anschluss.

### Reicht es? Die Bilanz über alle vier Ressourcen

Bedarf ist **65 Mux-Kanäle**, nicht 67: die zwei `REC`-Pads hängen an der
Taster-Kette, und `STAGES` teilt sich seinen Poti mit `ATTACK` — ein Poti, ein
Kanal.

> **Addendum 2026-09-28 (English): the demand is 70, not 65.** The 65 predates
> the 2026-08-30 recount in §1 (67 → 73 positions) and was never carried
> forward. `gen_hw_panel.py` today has 72 pot-class params on **70 pot
> positions** (`STAGES_A/B` share `ATTACK_A/B`), plus the three keycaps
> `REC_A/B` and `MODBTN`. Five 16:1 chips still carry it, with 10 spare instead
> of 15; nine 8:1 chips would carry it with 2 spare. The sweep length does not
> change (32 / 24 steps). Counted by `tools/scan_budget.py`, whose guard goes
> red when the plate moves — [`scan-budget.md`](scan-budget.md) §5. The table
> below is left as it was written; its mux row read 70 / 10 on that day
> (today's count is in the note below).

> **Nachtrag 2026-10-08: die 9-mm-Korrektur hat den Bedarf auf 73 Positionen
> gebracht.** Die Platte hat jetzt **73 Poti-Positionen** (drei reservierte
> Potis `ROOT_A`, `ROOT_B`, `REV_MOD` zählen mit: sie schicken nichts, werden
> aber über einen Mux-Kanal gelesen), statt der 70 des Addendums oben.
> `tools/scan_budget.py` druckt für 73: fünf 16:1-Chips mit 32 Schritten oder
> **zehn** 8:1-Chips mit 24 Schritten (48 ms pro Sweep bei einem Schritt pro
> Block). Rev A baut die zehn 8:1-Chips; zusammen mit den zwei
> Kalibrierkanälen `CAL_GND` und `CAL_3V3` sind das **75 von 80 Eingängen, 5
> frei** (`hardware/reva/panel-map.json`) — nicht mehr „neun 8:1-Chips mit 2
> frei“. Die 595-Zeile der Tabelle unten zählt noch 19 LEDs; es sind 15
> (`panel-map.json`), und ihre fünf Enables sind seit P2 zehn (ein Enable je
> Mux, `shell/mux_plan.h`); die Adress- und Enable-Spalte ist hier nicht neu
> gerechnet.

| Ressource | Kapazität | Bedarf | Rest |
|---|---:|---:|---:|
| Sense-Pins (ADC, **nicht** aus dem GPIO-Pool) | 4 | 4 | 0 |
| GPIO-Pool | 10 | 10 | **0** |
| Mux-Kanäle (5 × 16:1 auf 4 Sense-Pins) | 80 | 65 | 15 |
| 595-Ausgänge (4 Register) | 32 | 19 LEDs + 4 Adressen + 5 Enables = 28 | 4 |
| 165-Eingänge | 24 | 4 Taster | 20 |

Die 595-Zeile ist hier **hergeleitet, nicht aus der Spec zitiert**, und sie
ist am 2026-08-19 nach unten korrigiert worden. Sie stand mit **21** LEDs, der
Zahl aus der LED-Feedback-Spec (`2026-08-16-led-feedback-design.md` §3/§9) —
aber das ist die Zahl des **Rack**-Panels. Die Hardwareplatte zeichnet **19**:
`_SKIP_HW_LIGHTS` in `gen_hw_panel.py` lässt `FLOW_A_L` und `FLOW_B_L` dort
bewusst weg, und `python res/gen_hw_panel.py` druckt entsprechend `lights=19`.
Es ist genau der Fehler, vor dem §1 warnt — eine Zahl aus einem Dokument statt
aus einem Lauf.

Die Rechnung nimmt einen Enable je Mux an; mit einem Dekoder wären es weniger.
Bei 16:1-Muxen sind 28 der 32 Ausgänge belegt, das vierte Register ist also
gebraucht und **vier Ausgänge bleiben frei** (nicht zwei). Die
3-Register-Rechnung von vor der LED-Feedback-Runde (10 LEDs, 19 von 24
Ausgängen) ist überholt.

**Und die Folgerung für 8:1 kippt mit der Korrektur:** neun Muxe statt fünf
heißen neun statt fünf Enables, also 19 + 3 Adressen + 9 Enables = **31 von
32** — das passt in die vier Register. Der Satz, der hier stand, verlangte ein
**fünftes** 74HC595; das war eine Folge der 21. Die 8:1-gegen-16:1-Frage bleibt
offen (§6), aber sie kostet kein Bauteil mehr.

**Das Ergebnis ist also: es reicht, mit Luft in jeder Zeile außer den Pins
selbst** — und die Null dort ist die geplante Null. Die zwei Dinge, die es
kippen könnten, sind kein Pin-Problem: die ungemessene Einschwingzeit pro
Kanal (§6) und der selbst zu schreibende Mux-Scan (oben).

### LED-Ausbau: was ein weiteres Register bringt

Gefragt am 2026-08-16, **bevor** die LED-Feedback-Runde lief: RATE, MOD, TIME
und LVL je Deck, dazu TIDE und PACE (TEMPO hatte schon eine LED). Gebaut wurde
am selben Tag mehr als das — **21 Lampen** statt der damals gezählten zehn (§3),
zwei davon frei geworden durch das Löschen der Capture-Anzeigen. Was hier steht,
ist deshalb keine Planung mehr, sondern die Rechnung für den *nächsten* Schritt:
was ein **fünftes** Register brächte.

| | heute (21 Lampen) | mit acht weiteren |
|---|---:|---:|
| 595-Ausgänge nötig (LEDs + 4 Adressen + 5 Enables) | 30 | **38** |
| Register à 8 Ausgänge | 4 (32) | **5 (40)** |
| GPIOs | 4 | **4** |

**Hardwareseitig ist jede Ausbaustufe ein Bauteil.** Ein weiteres 74HC595 in die
bestehende Kette, dazu die LEDs mit Vorwiderständen — **keine GPIOs**, genau
dafür ist die Kette da. Das vierte Register ist dabei kein Ausbau mehr, sondern
Bestand: 30 der 32 Ausgänge sind belegt (§3). Beim Verteilen nicht alle auf ein
Register hängen (Paket-Gesamtstrom);
das ist eine Datenblattfrage beim Bestellen, keine Architekturfrage. Jedes
weitere Register sind wieder 8 LEDs, weiterhin ohne einen einzigen Pin — die
praktische Grenze ist die Kettenlänge und der Strom, nicht das Board.

**CPU-seitig kostet An/Aus nichts.** Eine Schieberegisterkette wird immer ganz
geschrieben, gleich wie viele ihrer Bits LEDs sind; von 32 auf 40 Bit sind acht
zusätzliche Schiebetakte pro Schreibvorgang. Und weil die Mux-Adressen auf
derselben Kette liegen, **wird die Kette ohnehin bei jedem Adressschritt neu
geschrieben** — die LED-Daten fahren mit.

**Daraus folgt, dass auch Helligkeit fast umsonst ist:** der Mux-Scan schreibt
die Kette 16× pro Sweep, einmal je Adresse. Variiert man über diese 16
Schreibvorgänge, welche LED-Bits gesetzt sind, ergibt das **16-stufiges PWM ohne
einen einzigen zusätzlichen Schreibvorgang** — Auflösung = Adressschritte,
Bildwiederholrate = Sweep-Rate. Die LED-Feedback-Runde hat genau darauf gebaut:
`spkyled::duty()` nimmt die Stufenzahl als Parameter, weil die 8:1-gegen-16:1-Wahl
(§6) sie bestimmt, und der Rack-Host quantisiert auf dieselben 16 Stufen, damit
er nicht feiner atmet als das Panel je kann.

**Die Grenze, und sie ist scharf:** wer *feinere* Helligkeit als 16 Stufen will,
muss das PWM vom Scan entkoppeln, und dann sind es echte zusätzliche
Kettenschreibvorgänge pro Block. Das kostet CPU und zahlt auf den Block-Artefakt
ein (§6) — 32 → 40 Bit ist marginal, eine eigene PWM-Schleife wäre es nicht.

**Alles in diesem Abschnitt ist hergeleitet, nicht gemessen.** Zu messen ist die
Kettenschreibzeit bei 40 gegen 32 Bit auf dem Board.

**Engine-seitig war doch etwas zu bauen.** Der Absatz, der hier stand, hielt
`lane_output`, `target_value`, `gate` und `pitch_gate` für ausreichend. Das war
falsch: `target_value` ist Knopf **plus** Modulation und hätte damit die
Knopfstellung angezeigt — genau das, was die Anzeige nicht zeigen soll. Die
LED-Feedback-Runde hat zwei const-Beobachter ergänzt:
`lane_excursion(part, lane)` für den Modulationsanteil allein
(`engine/instrument.h:422`, aus `Part::target_raw` herausgezogen, damit Lampe und
Audiopfad denselben Ausdruck lesen) und `limiter_squash()` für den Master-Former
(`:306`). Die Zuordnung auf Lampen liegt in `host/vcv/src/led_law.hpp`, ist
Rack-frei und damit für die Firmware wiederverwendbar — wo die Datei am Ende
liegt, entscheidet die M6-Inbetriebnahme.

**Die Instrumentenfrage ist entschieden.** Eine Lampe zeigt die
**Lane-Bewegung**, nicht die Knopfstellung — die sieht man am Knopf. Und sie
zeigt sie über **Helligkeit**, nicht als Blitz pro Zyklus: eine Hüllkurve setzt
die Obergrenze, die Momentanauslenkung atmet darin, und dunkel heißt genau eine
Sache, nämlich dass hier nichts moduliert. Siehe
[`2026-08-16-led-feedback-design.md`](../superpowers/specs/2026-08-16-led-feedback-design.md)
§1/§10 und [`docs/roadmap.md`](../roadmap.md).

## 4. Die geometrische Kapazität

**Diese Frage ist beantwortet, und zwar durch Zeichnen statt durch Rechnen.**
Der Abschnitt stand ursprünglich hier, um für 42 HP eine Obergrenze aus einem
Rasterüberschlag zu gewinnen (98 Plätze bei 15 mm, 45 bei 22 mm). Das Panel ist
inzwischen gezeichnet, generiert und gegen seine eigenen Keep-outs geprüft:

- Plattenmaß **304,8 × 128,5 mm** (60 HP, 3 HE) — `HP = 60`,
  `W = HP * MM_PER_HP`, `Hh = 128.5` in `gen_hw_panel.py`.
- Bedienelemente laufen von **y = 14,5 mm** (obere Reihe) bis **y = 97 mm**, auf
  neun Linien (14,5 / 34 / 50,22 / 53 / 74,4 / 79 / 89,86 / 95 / 97); waagerecht
  von x = 16,25 bis x = 288,55, beide Ränder von `ENGINE_A/B`. Darunter die
  Buchsenreihe bei **y = 114 mm**, in der auch das reservierte Pad, der SD-Slot
  und — als einziger Parameter außerhalb der neun Linien — `MODBTN` bei
  x = 290,8 sitzen.
- Untergebracht sind **73 Poti-/Taster-Positionen** (72 auf den neun Linien,
  dazu `MODBTN` in der Buchsenreihe), **1 reserviertes Pad, 19 LEDs,
  18 Buchsen und der SD-Slot** — 19, nicht die 21 der LED-Spec, weil die
  Hardwareplatte `FLOW_A_L`/`FLOW_B_L` nicht zeichnet (§3) — geprüft von
  `hw_panel_guard`: Schienen-Keepout,
  Überlappung nach echten Bauteilradien, ein Beschriftungsabstand für alle
  Klassen, Legenden gegen den 8,03-mm-Rack-Jack-Körper, SD-Ausschnitt frei,
  Spiegelsymmetrie — und dass die eingecheckten Dateien dem entsprechen, was der
  Generator heute erzeugt.

Der Rasterüberschlag von 2026-08-08 ist damit historisch und wird hier nicht auf
60 HP hochgerechnet — er würde eine Zahl liefern, die weniger wert ist als die
gezeichnete Platte.

## 5. Die Buchsen

**18 Buchsen: 12 Eingänge, 6 Ausgänge** (`gen_hw_panel.py`, gemessen
2026-08-16). Die acht MOD-CV-Eingänge existieren nur auf dem Hardware-Panel
(Spec 2026-08-10 §4); im VCV-Modul sind es vier Eingänge.

| Buchse | Art | liegt auf | Anmerkung |
|---|---|---|---|
| `IN_L`, `IN_R` | Audio in | B4/B3 | auf dem Submodule vorhanden |
| `CLOCK`, `RESET` | Gate/Trigger in | B10/B9 (Gate In 1/2) | `GateIn`, **digital** — Gates und Trigger, keine analoge Clock-Spannung |
| `MOD1..4_A`, `MOD1..4_B` | CV in | `CV_1..8` (C2–C9) | bipolar konditioniert (`InitBipolarCv`: ±5 V, invertiert, 2 ms Slew) — als Poti-Sense verworfen, **hier genau richtig** |
| `OUT_L`, `OUT_R` | Audio out | B2/B1 | auf dem Submodule vorhanden |
| `GATE_A`, `GATE_B` | Gate out | B5/B6 (Gate Out 1/2) | |
| `PITCH_A`, `PITCH_B` | CV out | C1/C10 (CV Out 1/2) | **hier klemmt es** |

Audio-I/O und die CV-Wandler sind auf dem Submodule bereits vorhanden — das ist
der Grund, dieses Modul zu nehmen, und es muss in der Rechnung auftauchen. **Das
ganze Buchsenfeld bildet 1:1 auf Modulpins ab, ohne eine einzige externe
Wandlerstufe.**

**Die CV-Eingänge laufen auf Blockrate, nicht auf Audiorate.** libDaisy setzt
`callback_rate_ = AudioSampleRate() / AudioBlockSize()` und aktualisiert die
`AnalogControl`-Objekte damit. **Achtung, gemessen statt angenommen:** die
Config im Quelltext trägt `blocksize = 48` (`daisy_patch_sm.cpp:294`), das Board
hat auf Nachfrage aber **96** gemeldet — bei 48 kHz also **500 Hz**
Aktualisierungsrate. Genau diese Annahme ist am 2026-08-08 einmal schiefgegangen
(aus Phasendauern auf 48 Samples geschlossen); seitdem fragt `shell/main.cpp`
die Blockgröße ab, statt sie zu setzen.

**Die Lücke, unverändert seit 2026-08-08 — und sie ist nicht die, für die man
sie beim Überfliegen hält.** Zwei Pitch- **und** zwei Gate-Ausgänge gehen: die
Gates sind GPIOs auf B5/B6 (`gate_out_1.Init(B5, GPIO::Mode::OUTPUT)`), die
zwei CVs hängen an einem 12-bit-DAC im DMA-Betrieb bei 48 kHz, der den zuletzt
geschriebenen Wert hält. Es ist exakt das Budget, und danach ist es leer. Zwei
Einschränkungen, beide aus `daisy_patch_sm.cpp` gelesen, nicht geschätzt:

- **0–5 V, hart geklemmt.** `VoltageToCode` rechnet `input * 819` und klemmt auf
  0..4095, Vollausschlag also exakt 5,000 V. Bei 1 V/Oktave sind das **fünf
  Oktaven und keine negative Spannung** — was darunter liegt, klebt auf 0 statt
  überzulaufen.
- **Kein dritter CV-Ausgang.** Eine Lane als CV, Velocity oder der STEP-Accent
  als Spannung, ein Clock-Out: dafür ist nichts mehr da.

Die Auflösung ist dabei *nicht* das Problem: 819 Codes pro Volt sind 1,22 mV
pro Schritt, rund **1,47 Cent**. Entscheidung der Envelope-Spec: dabei bleiben,
dokumentiert. Der Ausweg (externer DAC, `MAX11300`) kostet SPI2 und damit zwei
Sense-Pins, also die halbe Poti-Kapazität.

**SD-Slot, 4-bit, nicht 1-bit.** Die Sampler-Engine lädt User-Samples von SD
(`src/hw/card.h`), und der Daisy-Bootloader flasht Firmware per Drag & Drop von
der Karte — **aber nur bei voll verdrahtetem 4-bit-Bus**. Für ein Gerät ohne
SWD-Pins ist das der zweite Update-Pfad neben USB-DFU und allein den Mehraufwand
wert. Auf dem Panel: 11 × 6 mm bei x = 152,4 mm in der Buchsenreihe,
frontzugänglich.

## 6. Was hier bewusst NICHT steht

Die Liste von 2026-08-08 nannte an erster Stelle die Einstufung der Parameter.
**Die ist entschieden und steht in §2.** Offen ist heute:

- **Die Einschwingzeit pro Mux-Kanal.** Task 6 Schritt 5b des Phase-0-Plans.
  Ohne sie ist keine Panelgröße gegen das Audio-Budget gegengerechnet — das ist
  die einzige *Zahl* in diesem Dokument, an der die 67 Positionen noch scheitern
  könnten.

  > **Nachtrag 2026-08-30: die Papierhälfte ist gerechnet, und sie ist
  > deutlicher ausgefallen als erwartet** —
  > [`settle-budget.md`](settle-budget.md), Skript
  > [`tools/settle_budget.py`](../../tools/settle_budget.py) mit Guard.
  > **Das ist Arithmetik und keine Messung**, 5b bleibt also offen; aber 5b ist
  > damit keine Halbierungssuche mehr, sondern eine Vorhersage zum Bestätigen:
  > bei 10 kΩ, nichts am `COM`, `SPEED_16CYCLES_5` muss ein Kanalwechsel nach
  > **1,6 µs** sauber sein. Drei Ergebnisse betreffen dieses Dokument direkt:
  >
  > 1. **Der Kondensator am `COM` fällt ganz weg**, er wird nicht kleiner. Jede
  >    Bestückung ist schlechter als keine — die Envelope-Spec sagt „≤ 1 nF oder
  >    weg", die Rechnung sagt weg.
  > 2. **Der Poti-Wert ist die eigentliche Entscheidung, und sie ist auf 10 k
  >    gefallen.** Ab 50 kΩ kippt der 16:1 über eine Klippe. Der Preis für 10 k
  >    ist Strom — 65 Potis ziehen ~21 mA dauerhaft auf 3V3 (20 k → ~11 mA);
  >    das war das einzige Argument für 20 k, und es trägt nicht (siehe den
  >    Nachtrag zur Versorgung unten).
  > 3. **Nicht die Ladezeit des ADC setzt das Sample-Fenster, sondern die
  >    Ladungsumverteilung** aus dem vorigen Kanal. Daraus folgt ein konkreter
  >    Firmware-Wert: das libDaisy-Default `SPEED_8CYCLES_5` ist in jedem
  >    gerechneten Fall zu kurz, mindestens `SPEED_16CYCLES_5`.
  >
  > **Und eine Zahl, die hier und im Capture herumgetragen wird, ist zu
  > pessimistisch:** die „~15,6 Hz pro Kanal" gelten für *einen Schritt pro
  > Block*, so wie gemessen wurde. Ein **vollständiger** Sweep passt bei 10 kΩ in
  > 0,16 Blöcke, die Obergrenze ist also die Blockrate selbst — **~500 Hz pro
  > Kanal**, das Zweiunddreißigfache.
  >
  > **Gemessen wird auf dem Testcoupon, nicht am Steckbrett** (entschieden
  > 2026-08-30). Das Modell ist linear in der Node-Kapazität, ein Jumper-Node
  > ist ein unbekanntes Vielfaches der angesetzten 65 pF — und für Übersprechen
  > und Rauschen neben dem Audiopfad wäre ein Steckbrett-Pass nicht einmal
  > konservativ. Die acht Punkte, die der Coupon dafür **vor** dem Layout
  > tragen muss, stehen in der Envelope-Spec §5 (Nachtrag 2026-08-30).
  >
  > **Nachtrag zur Versorgung, 2026-08-30, und er schließt den Posten:** das
  > Patch-SM-Datenblatt (v1.0.5, Table 1 — *Absolute Maximum Ratings*) gibt
  > **3V3 Output = 500 mA**, 5V Output = 800 mA, mit der Fußnote „Maximum
  > output current is firmware dependent". Die ~21 mA der 10-k-Potis sind davon
  > **4 %**. Zwei Einschränkungen der Vollständigkeit halber: es ist die
  > Absolute-Maximum-Tabelle und keine Betriebsangabe, und der Eigenverbrauch
  > des Moduls (H750 bei 480 MHz, SDRAM, Codec, USB) kommt aus demselben
  > Budget und **steht im Datenblatt nirgends**. Die belastbare Aussage ist
  > „21 mA sind nicht das Problem", nicht „479 mA sind frei".
  >
  > **Zwei Nebenfunde aus demselben Datenblatt, beide entscheidungsrelevant.**
  > Erstens nennt Electrosmiths eigenes Potentiometer-Anwendungsbeispiel als
  > Beispielteil ein **Alpha 9 mm Linear 10K** (`RD901F-40-15F-B10K-00D70`) —
  > der Herstellerreferenzentwurf landet unabhängig auf demselben Wert wie die
  > Rechnung. Zweitens, und das schließt eine Option, die sonst naheliegt:
  >
  > > „When using ADC_9 to ADC_1 2, use +3V3 OUT (A1 0) instead of +5V OUT (A6)."
  >
  > `ADC_9`–`ADC_12` sind genau die vier Sense-Pins A2/A3/D8/D9 (§3). Die
  > Potis auf einen **eigenen** 3,3-V-Regler der Control-PCB zu legen, um den
  > Modulregler zu entlasten, ist damit falsch: die Wandlung ist ratiometrisch
  > zur ADC-Referenz, und die Differenz eines zweiten Reglers zu dieser
  > Referenz erscheint als Verstärkungsfehler und als Rauschen in jedem
  > Messwert. Die Potis hängen an **A10**. (`VREFBUF` wird von libDaisy
  > nirgends konfiguriert — geprüft; wie das Board `VREF+` beschaltet, ist von
  > hier aus nicht prüfbar, die Anweisung steht aber für sich.)

  > **Addendum 2026-09-28 (English, like everything added to the repo since):
  > 5b is measured and closed.** The test coupon measured the settle time on
  > fixed dividers (2026-09-17/18, [`settle-measured.md`](settle-measured.md))
  > and then on real pots at mid travel (2026-09-28,
  > [`pots-measured.md`](pots-measured.md) §11). Largest true settle seen:
  > **4067, 10 k pot ≤ 2.8 µs; 4067, 20 k pot ≤ 4.8 µs; 4051, 10 k pot
  > ≤ 2.0 µs** — against the 1.6 µs the paper half above predicted for 10 k
  > (the model is 1.7–2.1× short for 10 k pots). A second finding matters here
  > at least as much: read once per audio block at the working sampling rung,
  > a 20 k pot at mid travel reads ~650 counts low; the 387.5-cycle rung
  > removes that at every wait (`wait-measured.md`, `pots-measured.md` §7).
  > **What is not done:** the panel's channel count has not been re-costed
  > against the audio budget with these constants and the long rung's
  > ~63 µs per conversion. That is the scan-budget pass, still open.
  >
  > **Addendum, later on 2026-09-28: the scan-budget pass is done** —
  > [`scan-budget.md`](scan-budget.md), script `tools/scan_budget.py`, guard in
  > ctest. The long rung is not needed: the shell's existing pattern (libDaisy's
  > free-running DMA, 12 channels, `SPEED_16CYCLES_5`, `OVS_32`) never idles,
  > reads at pot impedance what the long rung reads, and fits one mux step per
  > audio block with ~300 µs to spare at no measurable CPU. Full sweep 64 ms on
  > the 16:1, 48 ms on the 8:1. A blocking long-rung read in the callback would
  > cost 13 points against the 2.9-point reserve. The verdict rests on the
  > oversampling order, which is documented by the HAL and not measured; the
  > panel scan's first coupon run tests it (`scan-budget.md` §7).
  >
  > **Addendum, later still on 2026-09-28: that run is done** — clean at one
  > step per block on every coupon channel, with the engine running at the
  > fixed operating point ([`scan-measured.md`](scan-measured.md)).
- **Der Mux-Scan selbst.** libDaisys `InitMux` kann 8:1 an GPIOs, gebraucht wird
  16:1 mit Adressen aus der 595-Kette (§3). Die Umschaltung muss geschrieben
  werden. **Die CPU-Seite ist seit dem 2026-08-23 nicht mehr offen, sondern
  gemessen** — sechs Läufe auf `patch_sm 3859386B3330`, `-O3`, Capture
  [`2026-08-23-978cbaf-shell-mux-placement.md`](../bench/2026-08-23-978cbaf-shell-mux-placement.md).
  32 gebitbangte Kettenbits plus vier ADC-Reads **pro Block** liegen unter der
  Auflösung der Messung (Lauf-zu-Lauf-Streuung 0,03 Punkte, der gemessene
  Aufschlag im Callback ist −0,10 auf `max`, also negativ und damit nicht
  physikalisch). Offen an diesem Posten bleibt die Anwendungsseite
  (`map_control` über 67 Kanäle, nicht gepreist) — und das war nie die Gefahr.
  Was der Scan im *Audio* anrichtet, ist eine andere Frage und steht unten unter
  Punkt 2.
- **Die Wahl 8:1 gegen 16:1.** Hängt an Verfügbarkeit und Bestückungspreis.
  **Nachtrag 2026-08-30: die Zeit entscheidet sie nicht** — der 4051 gewinnt
  zwar doppelt (halbe `C_COM`, und neun Chips verteilen sich mit 24 Schritten
  besser auf vier Sense-Pins als fünf mit 32), aber bei 10 k und 20 k liegen
  beide bequem in einem Audioblock. Erst ab 50 kΩ wird daraus eine Zeitfrage.
  Die Entscheidung bleibt also, wo sie steht: Verfügbarkeit, Preis, und
  595-Ausgänge (28 gegen 31 von 32). Siehe
  [`settle-budget.md`](settle-budget.md) Befund 5.

### Ist das eine Zeit- oder eine Machbarkeitsfrage?

Gestellt am 2026-08-16, weil die zwei Posten oben zusammen nach mehr klingen
als nach Fleißarbeit. **Antwort: überwiegend Zeit, aber nicht ausschließlich.**

**Wofür die Machbarkeit spricht:** 16:1-Muxe an einem ADC sind das
Standardverfahren jedes Hardware-Synths. Der Entwurf ist elektrisch richtig,
die Kapazität passt mit Reserve in jeder Zeile (§3), und der DMA-Scan der
`AdcHandle` bleibt nutzbar — es fehlt die Kanalumschaltung, nicht das Konzept.

**Drei Stellen, an denen es trotzdem klemmen kann, nach Ernst sortiert:**

1. **Das CPU-Budget — war als „die reale Gefahr" eingestuft, und ist es nicht.**

   > **Gemessen 2026-08-23, und damit ist dieser Punkt erledigt:**
   > `docs/bench/2026-08-23-978cbaf-shell-mux-placement.md`. Der Scan im
   > Audio-Callback, ein Schritt pro Block, kostet **weniger als die Messung
   > auflöst** — die Streuung zwischen zwei Läufen desselben Images ist 0,03
   > Punkte, und der „Aufschlag" kommt mit −0,10 auf `max` negativ heraus. Auf
   > die 2,9 Punkte Reserve unten wirkt das nicht, und zwar um mehr als eine
   > Größenordnung nicht. Die Übertragung auf den Bench-Worst-Case ist
   > zulässig, weil die Arbeit pro Block fest ist und nicht davon abhängt, was
   > die Engine tut; die Basis selbst ist **nicht** übertragbar (76,7 % ist der
   > eine Betriebspunkt des Shells auf SYNTH, nicht `instrument_worst_bbd_dtcm`).
   >
   > **Und die Platzierungsfrage ist beantwortet:** der Vordergrund-Scan hat in
   > beiden Läufen `steps=2500` gegen `blocks=2500` geschafft — keine einzige
   > verpasste Schrittgelegenheit — bei Callback-Last auf Basisniveau. Der Scan
   > **muss** nicht in den Callback, und außerhalb belastet er das Audio-Budget
   > gar nicht. Der Absatz unten ist ab hier Historie: er beschreibt, was
   > befürchtet wurde.

   Der Gate `instrument_worst_bbd_dtcm`
   steht auf dem Submodule bei **97,02–97,16 % `pct_max`, also ~2,9 Punkte
   Reserve** — direkt gemessen am 2026-08-19
   (`docs/bench/2026-08-19-3def5d5-feed-axi-o2-patch_sm-usb.md`, zwei Läufe).
   Hier stand vorher 2,17 Punkte, vom **Seed** hochgerechnet über
   `docs/bench/2026-08-07-seed-vs-patch-sm.md` (dort 96,43 % auf dem Seed); die
   Hochrechnung ist durch die direkte Messung ersetzt und lag konservativ. Ein pro Block
   gebitbangter Ketten-Write plus Kanalauswertung landet genau in dieser
   Reserve. Beherrschbar — ein voller Sweep muss nicht jeden Block laufen, die
   Potis sind auch bei einem Sweep alle paar Blöcke schnell genug —, aber nicht
   gratis, und **ungemessen**. Wenn etwas den Plan kippt, dann das.

   > **Nachtrag 2026-08-23: dieser Absatz setzt still voraus, dass der Scan im
   > Audio-Callback sitzt, und genau die Frage hat nie jemand gestellt.** Ein
   > Vordergrund-Scan, getaktet auf einen Schritt pro Block, taucht im
   > `CpuLoadMeter` gar nicht auf — er verbraucht Leerlaufzeit, nicht
   > Callback-Zeit, und die Reserve oben wäre dann die falsche Zahl für dieses
   > Problem. Dass ein Schritt pro Block reicht, ist Arithmetik: 32 Schritte
   > (acht 16:1-Muxe) à 2 ms sind 64 ms für einen Vollscan, ~15,6 Hz pro Kanal;
   > mit vier Chips die Hälfte. Nebenbei fällt damit auch die Einschwingzeit
   > als Kostenposten weg — die Blockperiode **ist** das Einschwingfenster,
   > wenn die Adresse am Blockende geschrieben und am Blockanfang gelesen wird.
   > **Ob der Vordergrund mitkommt, ist am 2026-08-23 gemessen worden: er kommt
   > mit, vollständig** (`steps=2500` gegen `blocks=2500`, zwei Läufe).
   > Ob 2 ms als Einschwingfenster wirklich reichen, ist damit nicht gesagt —
   > das bleibt 5b.
2. **Der ungeklärte Block-Artefakt.** Auf dem Board liegt ein Störton auf der
   Blockrate, 28 dB über dem Desktop-Referenzpunkt. Zwei Messungen vom
   2026-08-08 sagen dazu: den Callback zwingen, nur Nullen zu schreiben, ändert
   den Pegel **gar nicht** (−59,5 dBFS in beiden Fällen); die Leerlaufzeit im
   Block mit einer `nop`-Schleife füllen, senkt ihn um **7,5 dB**. Der Störer
   nimmt also nicht den Signalweg, sondern hängt daran, **wie Rechenaktivität im
   Block verteilt ist** — und die Ursache ist bis heute nicht benannt. Eine
   periodische GPIO-Salve pro Block ist genau eine neue Quelle dieser Sorte.
   Das ist keine Spekulation über einen Zusammenhang, sondern die Fortschreibung
   einer vorliegenden Messung; ob sie eintritt, ist offen.

   > **Gemessen am 2026-08-23** auf dem Submodule mit den Buchsen
   > (`385138563330`, drei Bilder, zwei bis drei Aufnahmen je Bild, Interface-Gain
   > über alle Läufe unangetastet,
   > [`docs/bench/2026-08-23-978cbaf-shell-mux-placement.md`](../bench/2026-08-23-978cbaf-shell-mux-placement.md),
   > Befunde 4 bis 5c). Auflösung 0,15 dB.
   >
   > **Die Salve im Callback bewegt den Störton nicht.** Die 500-Hz-Reihe liegt
   > mit Scan bei −60,7 dBFS, ohne bei −60,6 — dieselbe Zahl. **Die Salve im
   > Vordergrund bewegt ihn sehr wohl: +7,3 dB auf der Reihe**, während der Rest
   > des Spektrums über alle drei Bilder gleich bleibt (−56,2 bis −56,9, kein
   > Trend). Der Anstieg ist also ausschließlich das Artefakt, nicht der Boden.
   >
   > Damit ist dieser Posten für die gewählte Platzierung erledigt und die
   > Fortschreibung oben war zutreffend — nur mit umgekehrtem Vorzeichen, als
   > der Absatz vermutete: gefährlich ist der Vordergrund, nicht der Callback.
   > Der Mechanismus bleibt unbenannt; ausgeschlossen ist allein die Schrittzahl,
   > beide Platzierungen taktten einen Schritt pro Block.
   >
   > **Der Störton selbst ist unverändert da.** Mit ausgeschaltetem Scan liegt
   > die 500-Hz-Reihe bei −60,8 dBFS und damit über ein 30-s-Fenster **9,2 dB
   > unter dem Programm** — hörbar als Dauerton, mit Harmonischen, die sich auf
   > das Synth-Signal legen. (Gegen die kurzen 8–10-s-Aufnahmen rechnete sich
   > 4 dB; das Programm schwankt sekundenweise um 6,5 dB, also gilt der längere
   > Wert.) Der Pegel der Reihe selbst ist über zwölf Aufnahmen des Tages
   > stabil auf −60,2 bis −61,2 — er folgt dem Interface-Gain und sonst nichts.
   > Das ist der Befund vom 8. August, ungemindert, und er gehört nicht zu dieser
   > Frage: er ist ohne jeden Mux da.
   >
   > **Am Abend des 2026-08-23 nachgemessen, und es sind drei Quellen**
   > ([`2026-08-23-978cbaf-artifact-triage.md`](../bench/2026-08-23-978cbaf-artifact-triage.md)):
   > die 500-Hz-Reihe hängt am Audioblock (mit gestopptem Audio fällt sie um
   > 30 dB), ein Cluster um **6,35 kHz ist der Schaltwandler des
   > MAX11300-Moduls** (38 dB Ablation — Modul drin −55,8, draußen −93,6; und
   > 31 dB lauter, nachdem das Modul einmal gezogen und wieder gesteckt wurde),
   > und USB steht mit seinem Start-of-Frame bei exakt 1 kHz, dreissig Dezibel
   > darunter. **Für die PCB-Regeln zählt vor allem der zweite Punkt:** neben
   > diesem Audioweg darf kein Schaltwandler auf derselben Versorgung hängen,
   > und ein Steckkontakt entscheidet über 31 dB.
3. **Die Einschwingzeit pro Kanal.** Sie entscheidet, wie viele Adressschritte
   pro Block gehen — nicht, ob es überhaupt geht. Der harmloseste der drei.

**Der Rückfallweg, falls 1 oder 2 zuschlagen** (Vorschlag, keine Entscheidung,
nirgends spezifiziert): ein Co-Controller auf der Control-PCB, der Potis und
Taster selbst scannt und die Werte seriell schickt. Dann braucht das Audio-MCU
**gar keine Sense-Pins mehr** — weder die vier rohen noch die Mux-Kette —, der
Scan-Aufwand verschwindet vollständig aus dem Audio-Budget, und A2/A3 werden als
UART frei, was sie von Haus aus sind. Kostet ein Bauteil und ein zweites
Firmware-Projekt.

**Fazit für die Planung:** die Machbarkeit steht nicht zur Debatte, es gibt
zwei Wege und der Rückfallweg ist der sauberere. Zur Debatte steht der Aufwand
und ob die dünnste Ressource des Projekts — die CPU-Reserve — ihn mitträgt.

> **Korrektur 2026-08-23.** Hier stand: „Das ist messbar, sobald ein Board mit
> Panel dranhängt, und vorher nicht." Der zweite Halbsatz ist falsch, und er
> hat die ganze Position teurer aussehen lassen, als sie ist. **Zwei der drei
> Posten oben brauchen kein Panel:** die Platzierungsfrage (Callback gegen
> Vordergrund) und der Block-Artefakt-Posten hängen an einer periodischen
> GPIO-Salve auf den vier Kettenpins — und die lässt sich auf dem
> unbestückten Submodule erzeugen, das seit dem 8. August auf dem Tisch liegt.
> Nur Punkt 3, die Einschwingzeit, braucht wirklich einen Mux am
> Steckbrett. Der Plan von diesem Tag misst deshalb die zwei billigen
> Posten sofort und lässt 5b liegen, bis die Teile da sind.
>
> **Was das entscheidet, ist nicht „mehr CPU sparen".** Die drei Ausgänge
> sind: die Platzierung (und damit, ob die CPU-Reserve für dieses Problem
> überhaupt die richtige Zahl ist), ob der Co-Controller in den Schaltplan der
> Control-PCB muss — eine Entscheidung, die **vor** der Bestellung fällt und
> danach nicht mehr —, und ob eine Ketten-Salve pro Block den Störton auf der
> Blockrate bewegt. Der dritte ist durch kein Sparen zu beheben; er wäre ein
> Befund über Aufbau und Entkopplung.
>
> **Stand 2026-08-23, nach beiden Messhälften:** alle drei Ausgänge sind
> beantwortet. Die Platzierung ist **der Audio-Callback** — er kostet nichts
> Messbares (unter 0,2 Punkten) und bewegt den Störton nicht, während der
> Vordergrund ihn um 7,3 dB anhebt. Damit spricht **weder aus CPU- noch aus
> Störton-Gründen** etwas für den Co-Controller; er bleibt ein Rückfallweg, den
> nichts mehr treibt, und muss nicht in den Schaltplan der Control-PCB. Offen
> bleibt nur Punkt 3, die Einschwingzeit, und die entscheidet 8:1 gegen 16:1,
> nicht das Prinzip.
>
> **Die ehrliche Grenze beider Hälften:** an den vier Pins hängt nichts.
> Der Treiberstrom ist damit kleiner als in der Serie, also ist der
> unveränderte Störton im Callback eine **untere Schranke und kein Freispruch**.
> Der verschlechterte im Vordergrund ist dagegen eindeutig — und er ist in der
> Serie eher größer. Sobald eine echte 595-Kette an B7/B8/D1/D10 hängt, ist die
> Callback-Messung zu wiederholen.
- ~~**Ob ein `MAX11300` das Buchsenfeld übernimmt.**~~ **Struck 2026-09-28
  (Bastian):** the MAX11300 was only on the August desk rig and is not part of
  the instrument. The jack field runs on the module's own pins, SPI2 stays
  free, and the envelope spec's rule stands.
- **Die exakte Pin-Map.** Task-2-Deliverable von Phase 0; die Envelope-Spec
  fixiert die Topologie, nicht die Pinnummern.
- **Das Plattenwort für BEND** (§2, letzter Absatz).

Nicht offen, sondern schlicht nicht begonnen: die Bring-up-Firmware selbst. Sie
hat keine Spec — siehe „M6 — Hardware prototype" in [`docs/roadmap.md`](../roadmap.md).
