mcbronkowitch/fireflow/hardware/reva/review.md

# FireFlow Rev A -- schematic review

Generated by `hardware/reva/build.py`; do not edit. The drawing: `python hardware/gen/check.py --project hardware/reva/build.py --full` writes `hardware/reva/out/reva.pdf` and one PNG per sheet.

212 parts (215 with power flags), 184 nets, 10 sheets under an overview.

## Sheets

| Sheet | Title | Parts |
|---|---|---|
| power | Eurorack power, reverse protection, 3V3D | 11 |
| module | Patch Submodule, sense pads, test points | 16 |
| mux_sense_0 | Pots on SENSE_0: U_MUX0, U_MUX1, U_MUX2 | 26 |
| mux_sense_2 | Pots on SENSE_2: U_MUX6, U_MUX7 | 18 |
| mux_sense_3 | Pots on SENSE_3: U_MUX8, U_MUX9 | 19 |
| mux_sense_1 | Pots on SENSE_1: U_MUX3, U_MUX4, U_MUX5 | 30 |
| chains | Shift-register chains and keys | 41 |
| leds | Panel LEDs | 30 |
| jacks | Jacks, straight to the module (patch.Init()) | 18 |
| sd | SD card, straight to the module (patch.Init()) | 3 |

## JLC assembly

10 lines, 74 parts. Extended types (one loading fee each, price read on the JLC page on the day): C5613 (Nexperia 74HC165D,653), C9386 (Nexperia 74HC4051D,653).

| LCSC | Type | Value | Qty |
|---|---|---|---|
| C15850 | Basic | 10u 25V | 3 |
| C14663 | Basic | 100n | 19 |
| C45783 | Basic | 22u 25V | 1 |
| C2480 | Basic | SS14 | 2 |
| C21190 | Basic | 1k | 28 |
| C25804 | Basic | 10k | 4 |
| C5613 | Extended | 74HC165 | 1 |
| C9386 | Extended | 74HC4051 | 10 |
| C6186 | Basic | AMS1117-3.3 | 1 |
| C5947 | Basic | 74HC595 | 5 |

## Hand-soldered

| Source | Part | Qty |
|---|---|---|
| Electrosmith | Patch Submodule, socketed | 1 |
| Thonk | 3 mm flat-top LED | 15 |
| Thonk | Alpha RD901F-40 9 mm, T18 shaft, B10K | 73 |
| Thonk | Thonk low-profile button, momentary; pin 1 closes to 2 | 4 |
| Thonk | Thonkiconn PJ398SM mono | 18 |
| hand-soldered | 2x5 female socket for the Patch SM, cut from a 2x10 strip; its holes belong to U_SM's footprint | 4 |
| hand-soldered | Yamaichi PJS008U-3000-0 vertical microSD, THT (P4-1 spec §4.2) | 1 |
| hand-soldered | shrouded keyed 2x5 box header; pin 1 = -12 V | 1 |

## Pot scan

| Sense pin | Muxes | Pots | Farthest pot from its mux group's centre |
|---|---|---|---|
| SENSE_0 | U_MUX0, U_MUX1, U_MUX2 | 20 | 31.9 mm |
| SENSE_2 | U_MUX6, U_MUX7 | 14 | 27.7 mm |
| SENSE_3 | U_MUX8, U_MUX9 | 15 | 36.8 mm |
| SENSE_1 | U_MUX3, U_MUX4, U_MUX5 | 24 | 41.1 mm |

## ERC waivers

| Type | Item | Count | Reason |
|---|---|---|---|
| pin_to_pin | `Symbol U_SM Pin D10 [SPI_SCK, Output, Line]` | 1 | D10 is a GPIO input in firmware (165 serial out); the symbol names its SPI_SCK default |
| pin_not_driven | `Symbol U_SR1 Pin 14 [SER, Input, Line]` | 1 | B7 drives SR_DATA push-pull as GPIO; the symbol names its I2C1_SCL default |
| pin_not_driven | `Symbol U_IN1 Pin 2 [CP, Input, Line]` | 1 | B8 drives SR_CLK push-pull as GPIO; the symbol names its I2C1_SDA default |

## Open items

- J_SD's footprint (Yamaichi PJS008U-3000-0) is generated from the EasyEDA footprint of LCSC C3177022, a secondary source; check it against a socket in hand before the order. The catalogue carries no LCSC number for J_SD: it is hand-soldered.
- P2's pin table calls C1 'CV out 1' and C10 'CV out 2'; the Patch SM datasheet names C1 CV_OUT_2 and C10 CV_OUT_1. The wiring (C1 = PITCH_A, C10 = PITCH_B) follows P2 by pin; P6's firmware table must follow the pins, not the names.
- AMS1117-3.3 output: 22 µF X5R MLCC (C45783). Stability with a low-ESR output capacitor is a bring-up check (P7), with the regulator's temperature at full LED load. C_LDO_T is fitted DNP (6032 low-ESR tantalum, ESR at most 0.5 Ohm per the AMS1117 datasheet); populate it if the regulator oscillates with the MLCC alone.
- SD card on SM_3V3 (A10): pot-scan noise while the card streams is a bring-up check. C_SD1 (100 nF) decouples the socket; C_SD2 (10 µF) is DNP, to fit if the scan shows card noise -- the module's TPS6213x allows 10-200 µF output capacitance with its 2.2 µH inductor.
- The key symbol (Switch:SW_Push_DPDT) draws pin 1 as the rest contact; Thonk's button closes 1-2 when pushed. The netlist is right at the pads (pin 2 common, pin 1 to the key net); read the printed keys as normally open.
- J_PWR pins 7/8 are left open, as on the coupon; the Doepfer A-100 bus has GND on 3-8 -- confirm against the actual bus board (carried from the coupon's TO CONFIRM).
- COM pads C_SENSE0-3 are fitted unpopulated (P2 §3).
- JLC stock is checked at the schematic freeze (13 Nov) and again before the order.
