mcbronkowitch/fireflow/docs/superpowers/specs/2026-09-30-rev-a-p4-2-routing-design.md

# FireFlow Rev A — P4-2: routing

**Date:** 2026-09-30
**Status:** approved in conversation (Bastian), section by section
**Parent:** the Rev A master plan
(`docs/superpowers/specs/2026-09-28-rev-a-master-plan-design.md`), sub-project
P4, the layout generator. Follows P4-1
(`docs/superpowers/specs/2026-09-29-rev-a-p4-1-placement-design.md`, merged
2026-09-30).

## 1. What P4-2 delivers

P4-2 turns P4-1's placed board into a routed, plane-filled, DRC-checked board:
`hardware/reva/kicad/reva.kicad_pcb`, byte-stable. It routes every net with our
own router (`hardware/gen/route.py`, chosen after the P4a spike) on 4 layers:
signals on F.Cu and B.Cu, GND on In1.Cu, SM_3V3 on In2.Cu. It adds the analog
rules the spike found missing (routing-spike findings 1 and 5), gates them with
checks that can each go red, and renders front and back on every run.

Like P4-1, P4-2 runs now, before the panel freeze (6 Nov). The panel pass is a
re-run, not hand work.

## 2. Decisions taken in brainstorming (Bastian, 2026-09-30)

1. **Audio clearance 10 mm**, the coupon's rule, measured outside the module's
   pad field. It is a design rule inherited from the coupon, not a measured
   coupling limit: the coupon's crosstalk probe measured ADC victims only.
   If the router cannot meet it, the run fails loudly and names the net; the
   number is then Bastian's call, not the implementer's.
2. **The rule applies per layer.** Copper on F.Cu and copper on B.Cu are
   separated by the In1.Cu GND plane. Across layers the audio nets must cross
   digital lines to reach the west jacks at all.
3. **Aggressors** (48 nets): the LED nets on both sides of the series resistor
   (`LED<n>`, `LED<n>_A`, n = 0..18), `SR_CLK`, `SR_DATA`, `SR_LATCH`,
   `SR_DIN`, and the SD bus (`SD_CK`, `SD_CMD`, `SD_D0`..`SD_D3`). Not
   aggressors: the mux address and enable lines (the coupon's crosstalk probe
   put them at the control floor) and the key lines (static).
4. **Victims** (4 nets): `OUT_L`, `OUT_R`, `IN_L`, `IN_R`.
5. **L/R spacing 2.0 mm** edge to edge, per layer, between `OUT_L` and `OUT_R`
   and between `IN_L` and `IN_R`. No guard track.
6. **SENSE nets are routed first, and each is at most 1.3 × its minimum
   spanning tree** (straight-line MST over its pads). Vias allowed. The coupon's
   "COM ≤ 15 mm, 0 vias, F.Cu only" does not carry over: on Rev A two or three
   muxes share one SENSE net (§3).
7. **No F.Cu copper under a pot body.** An Alpha 9 mm pot's two mounting tabs
   are the legs of a metal cover that sits flat on the board; mask alone
   (~20 µm) is not trusted against it. Under jack, LED and key bodies (plastic)
   F.Cu stays free to use.
8. **Known panel violations get a known list**, as in P4-1: a connection may
   stay unrouted, or a DRC item may stand, only if it touches the jack row,
   the SONG clusters or the two admitted LED/pot pairs. The list must be empty
   at the freeze.
9. **Approach A:** the rules live in the router; one run routes the whole
   board. Rejected: pre-routing the rule-bearing nets by scripted waypoints
   (they break on the panel pass, and the LED tracks need the pair rule
   anyway); Freerouting (decided against on 2026-09-29).

## 3. Measured facts this spec rests on

Probed on the committed P4-1 board (`hardware/reva/kicad/reva.kicad_pcb`,
2026-09-30):

- **189 nets** have two or more pads.
- **Audio routes are long.** OUT_L runs U_SM.B2 → J17.T, 89.2 mm straight;
  OUT_R U_SM.B1 → J18.T, 98.7 mm; IN_L and IN_R run from U_SM.B4/B3 to J1/J2 in
  the west, 140.3 and 141.9 mm. Along each straight line only 1–3 LED or
  SR_CLK pads lie within 10 mm, so the pads leave room; whether the router can
  keep the LED *tracks* away is what the first run shows.
- **At the module the rule cannot hold:** SR_CLK (U_SM.B8) sits 2.54–5.68 mm
  from the audio pins B1–B4. That is the module's pinout.
- **The module's pad field is two groups, not one box.**
  - The east header is 2 × 10 pads at x 177.63 / 180.17, at 2.54 mm pitch in
    two halves: y 46.17–56.33 and y 72.17–82.33, with a 15.84 mm gap. It
    carries B1–B10 and C1–C10. The lower half holds all four audio pins
    (x 180.17, y 74.71–82.33) and SR_CLK (B8, x 177.63, y 79.79).
  - The west pads are two rows of 5 at x 118.82–128.98, at y 48.98 and 79.52
    (the A and D pins).
  - Clustered at one pin pitch (2.54 mm), that is four groups. All 40 pads are
    THT (1.88 mm round).
  - One box around all 40 pads would be 61 × 36 mm and would exempt most of
    the module's footprint.
- **SENSE nets:**

  | Net | Pads | MST | Farthest pad from its module pin |
  |---|---|---|---|
  | SENSE_0 | 6 | 137.8 mm | 83.7 mm |
  | SENSE_1 | 6 | 245.0 mm | 166.4 mm |
  | SENSE_2 | 5 | 40.5 mm | 19.3 mm |
  | SENSE_3 | 5 | 111.9 mm | 58.5 mm |

  Node capacitance per `settle-budget.md`: 25–50 pF per mux, 15 pF stray
  (estimate). Track adds roughly 0.1 pF/mm (estimate, not measured), so
  SENSE_1's track is of the order of 25 pF.
- **J_SD pad pitch is 1.10 mm** (pads 1–8 at x 148.55–156.26). The router has
  never routed a pitch below the SOIC's 1.27 mm (spike known limit).
- **Supply nets** routed as tracks: `+12V` (6 pads), `-12V` (4), `3V3D` (26),
  plus `+12V_IN` and `-12V_IN` before the reverse diodes. `GND` and `SM_3V3`
  are planes.
- **kicad-cli's report** has the summary lines `** Found N DRC violations **`,
  `** Found N unconnected pads **`, `** Found N Footprint errors **` and
  `** End of Report **` (P4-1's report, 3444 lines).
- **KiCad 10's defaults differ from the board rules:** a fresh `BOARD()` has
  min track 0.2, min via 0.5, min clearance 0.0 mm; `kipcb.new_board` sets
  0.25 / 0.6 / 0.2. Only copper-to-edge (0.5 mm) matches. The committed
  `reva.kicad_pro` (P3's `build.py`) holds only `meta`.
- **Spike timing:** the P4a strip (97.1 × 116.1 mm, 47 nets) routed on 4 layers
  in 6.2 s at pitch 0.2 mm. The full board is about 3× the area with 189 nets.
- **Probed during execution (Task 1, 2026-09-30): full-board runtime.** The
  unmodified router on the whole placed board, alone on an idle machine:
  `nets 187 failed 18 [CLOCK, GATE_A, GATE_B, IN_L, IN_R, MOD1_A..MOD4_A,
  MOD1_B..MOD4_B, OUT_L, OUT_R, PITCH_A, PITCH_B, RESET] conflicts 2
  iterations 30 vias 425 length 8683.1 mm seconds 426.7`.
  - With `max_iters=1`: 20.2 s and 119 conflicts. The negotiation never
    converges, so all 30 rounds run.
  - A first measurement (464.9 s) overlapped other work on the machine and was
    discarded.
  - 187 nets, not 189: the two plane nets (GND, SM_3V3) are not routed.
- **Probed during execution (Task 1, 2026-09-30): J_SD terminals at pitch
  0.2.** Terminal cells per pad: SD_D2 (1) 2, SD_D3 (2) 2, SD_CMD (3) 2,
  SD_CK (5) 2, SD_D0 (7) 2, SD_D1 (8) 2. Minimum 2, none has 0, so §4.2.5's
  finer stub is not needed.
- **Probed during execution (Task 1, 2026-09-30): jack tip pads lie outside
  the grid.** All 18 failed nets are jack nets.
  - Each jack's tip pad T sits at y 118.92 (pad box y 117.86..119.98).
  - The router grid ends at y 118.5 (outline 119.25 − edge 0.5 − supply
    half-width 0.25).
  - `_terminal_cells` searches only ±2 cells (0.4 mm) around the rounded pad
    centre, so no terminal cell exists and all four audio nets are unrouted.
  - Answer: §4.2.6.
- **Probed during execution (Task 1, 2026-09-30): which `.kicad_pro` keys
  kicad-cli honours.** On the P4-1 board plus one 0.2 mm track on 3V3D:
  - A pro with `board.design_settings.rules` (plus `meta`) gives the same
    per-class DRC counts as the pro SaveBoard writes; `track_width` 1 with it,
    0 without.
  - Adding `net_settings` changes no count. The minimal key set is
    `board.design_settings.rules`: `min_track_width` 0.25,
    `min_via_diameter` 0.6, `min_through_hole_diameter` 0.3,
    `min_clearance` 0.2, `min_copper_edge_clearance` 0.5.
  - `clearance` (8) and `copper_edge_clearance` (18) counts were the same
    without the rules; only the counts were compared.
- **Probed during execution (Task 6, 2026-09-30): pair-rule cost.** With pad
  shapes, the A* sped up (500.9 s for 30 rounds without pair rules), pair
  rules, module zones and tiers, one profiled round took 487.0 s: 419 s
  marking pair clearances around routed copper, 17 s path search.
  `failed ['LED16', 'LED16_A', 'OUT_R']` (the jack zones of §4.2.2 answer
  that). Bastian decided on 2026-09-30 to speed the marking up (same radii,
  default path byte for byte) before the first full run.
- **Probed during execution (Task 6, 2026-09-30): the router does not
  converge.** With every rule in place: 12 conflicts after 30 rounds,
  784.5 s. Tuning via cost and the negotiation parameters gave 15–22
  conflicts (four runs); ripping up every net each round gave 17. Switching
  single rules off (conflicts only; the runs shared the CPU): no pair rule 9,
  no via keepouts 15, one tier 7 (IN_L and IN_R then fail). No single rule
  causes it. The conflicts sit in x 104–152, y 29–75, where the P4-1 placement
  put 146 pads on 2208 mm² (0.066 per mm², against 0.028 over the whole
  board): U_SR1–3, U_IN1, U_MUX7, part of U_MUX6, and the module's west pins,
  under ten pots. Bastian decided on 2026-09-30 to spread the placement there
  through P4-1's `OVERRIDES` (P4-1 spec §4.4), with the panel untouched.
- **Measured during execution (Tasks 6a and 6b, 2026-10-01):**
  - Placement was spread through `OVERRIDES` twice. Task 6a thinned the dense
    field (x 104–152, y 29–75) from 146 to 100 pads; the router's conflicts
    after 30 rounds went from 12 to 0. Task 6b, after §4.2.9, moved the
    plane-net pads clear of the pot bodies: U_SR3 to (84, 73) rotated 90°,
    U_IN1 8 mm south. The escape stubs under pot bodies (U_SR3.8 GND
    5.70 mm under RV22, C22.2 GND 3.36 mm under RV40) are gone, and C19.2,
    boxed in before, is stitched.
  - `place.py` reserves a decoupler's room only against the parts placed
    before its IC. With only U_IN1 moved, the run stopped with "no free place
    for C17"; U_SR1 is pinned by an override to work around it.
  - The offsets of U_SR5, R1–R3 and R12 ride on anchors that follow U_SR1 and
    U_IN1. Re-derive them whenever those two move.
  - U_REG moved 22.5 mm in Task 6b and now sits 17.4 mm from J_PWR. No check
    gates that distance.
  - The router leaves T-junctions: a branch can end on the middle of a host
    segment. kicad-cli flagged two of them as `track_dangling` once (Task 6b,
    run 2), and none of the 46 on the final board. `track_dangling` is gated.

## 4. Design

### 4.1 Pipeline and files

**place → route → check**, one process:

- `hardware/reva/place.py` is unchanged in what it places. `route.py` calls
  `place.build()` and routes that board in memory, so placement is always fresh.
- **New `hardware/reva/route.py`:**
  - builds the router's input from the placed board;
  - runs the router and writes the result back as tracks and vias;
  - stitches SMD pads on the plane nets to their planes (`stitch.py`,
    `netless_blocks=True`, routing-spike finding 8);
  - fills the zones and saves to `hardware/reva/out/reva-routed.kicad_pcb`;
  - runs `route_check.run()`, which renders front and back.
  - With `--write`, and only on a GREEN run, it copies the board to
    `hardware/reva/kicad/reva.kicad_pcb` and the renders to
    `docs/hardware/routing/`.
- **New `hardware/reva/route_check.py`:** the checks of §5, in P4-1's pattern.
- **New `hardware/reva/rules.py`:** every board rule in one place. That covers
  track widths per class, via, clearance, copper-to-edge, the pair rules, the
  aggressor and victim sets, the SENSE factor and the exemption margin.
  `place.py`, `route.py` and P3's `build.py` read from it.
  - The checks keep their own thresholds per the P4-1 constraint.
  - `route_check.py` does **not** import its limits from `rules.py` or
    `route.py`: it owns them, as `place_check.py` does.
- **The committed `reva.kicad_pro` carries the board rules.** `build.py`
  writes them, so the committed pair (`reva.kicad_pcb` + `reva.kicad_pro`) is
  judged by kicad-cli under the real rules. Which JSON keys kicad-cli honours
  is probed first (plan). The coupon's project file is untouched:
  `gen/check.write_project_file` keeps its default output.
- **Ownership of `reva.kicad_pcb` moves to `route.py`.**
  - `place.py --write` no longer copies to `kicad/`, and its renders go to
    `docs/hardware/placement/` as before.
  - `reva_place_guard` stops comparing the committed board and keeps every
    other assertion.
  - `test_build.py`'s exemption (`PLACED_BOARD`) names `route.py` as the
    owner.
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
