mcbronkowitch/fireflow/docs/superpowers/specs/2026-10-07-panel-nine-mm-raster-design.md

# Panel correction — the 9 mm raster

**Date:** 2026-10-07
**Phase:** Rev A P1 correction round (P1 spec `2026-09-29-rev-a-p1-panel-parts-design.md`
§5, "each failure gets a fix in the generator"), before the panel freeze
(`panel-freeze-2026-11-06`) and before the Rev A board is ordered.
**Trigger:** the acrylic plate arrived. Checklist items 1 and 2 of
`docs/hardware/grip-test.md` (pinch two neighbours, turn without brushing a
neighbour's cap) failed: the knobs stand too close to play. Item 3 (patching
all jacks) passed — the jack row was fine.
**Decisions (Bastian, 2026-10-07):** no two caps closer than **9 mm, edge to
edge**; spacing beats thematic grouping — form follows function. The plate
shows **timing, not modulation**. The Rev A board is not ordered yet, so the
board follows the plate. The distance from the knobs to the jacks stays as it
is: plugged cables are in the way of turning knobs.

This is also **the one panel pass** that P4-1 left its known panel violations
for (decided 2026-10-04): the jack row's height and the LED rework travel with
the knob raster, so the scripted chain to the board runs once.

## 1. Goal and scope

*Amended 2026-10-08 after Task 7a:* the smallest gap is 9.70 mm since the
centre re-pitch (§3); it was 10.27.

Every knob and key on the 60 HP plate keeps at least 9.0 mm between cap
edges, measured with the real caps — and the layout below delivers at least
9.70 mm. Deck B stays deck A mirrored; the centre column is mirror-symmetric
about the plate's centre line. The plate stays 60 HP.

Done means: the generator places every control from one cell table; a guard
proves the 9 mm rule and has been seen red once; the hole list, cut file,
print sheet, panel map, placed and routed Rev A board, order package,
generated firmware table and the VCV `FireflowHW` panel all come from the new
positions; every gate along that chain is green; and the board's
`KNOWN_PANEL` exemption sets (`place_check.py`, `route_check.py`) are empty
— except `route_check.py`'s `"audio"` set, which holds exactly the two
admitted jack-zone pairs (§5.3).

**In scope:** the knob raster (§3), three reserved knob positions (§4), the
LED inventory (§5), the jack row's height (§6), the group fields (§7), the
mux assignment rule (§8), and the chain to the board and the firmware (§10).

**Not in scope:** jack x positions and pitch (patching passed); the big VCV
module `Fireflow`; the engine; plate colours; key functions. **How** the LEDs
light is P6b's LED law and the VCV host's light code — §5 fixes what each one
*means*, this pass gives it a LightId, a position, a hole and a footprint.
**Making the reserved knobs real parameters** is a follow-up spec (§4).
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
