mcbronkowitch/fireflow/docs/hardware/placement/reva-placed-bottom.png

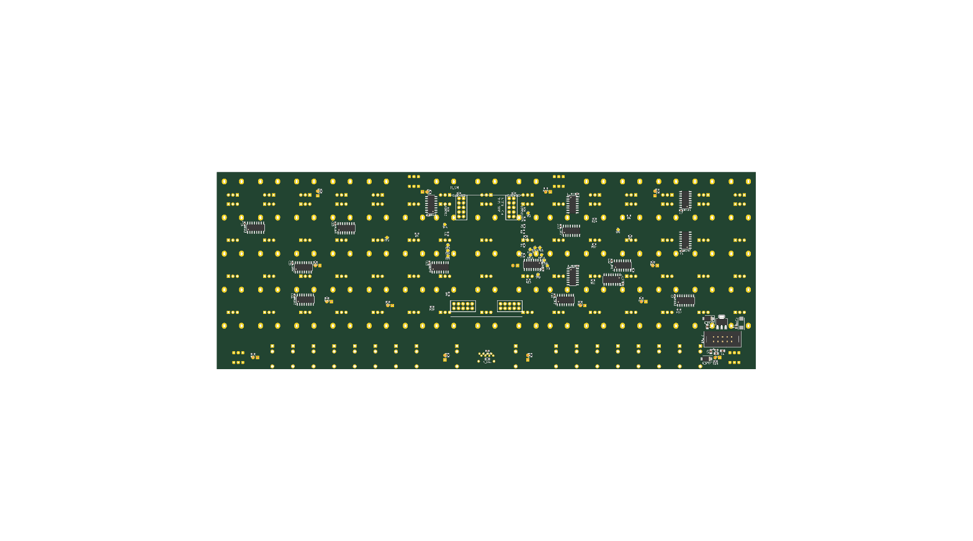
docs/hardware/placement/reva-placed-bottom.png
