mcbronkowitch/fireflow/hardware/coupon/proof/coupon-board-back.png

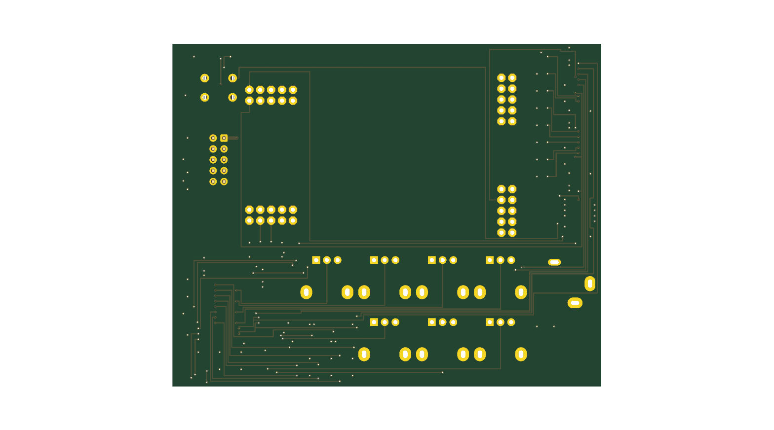
hardware/coupon/proof/coupon-board-back.png
