mcbronkowitch/fireflow/hardware/coupon/proof/coupon-board-front.png

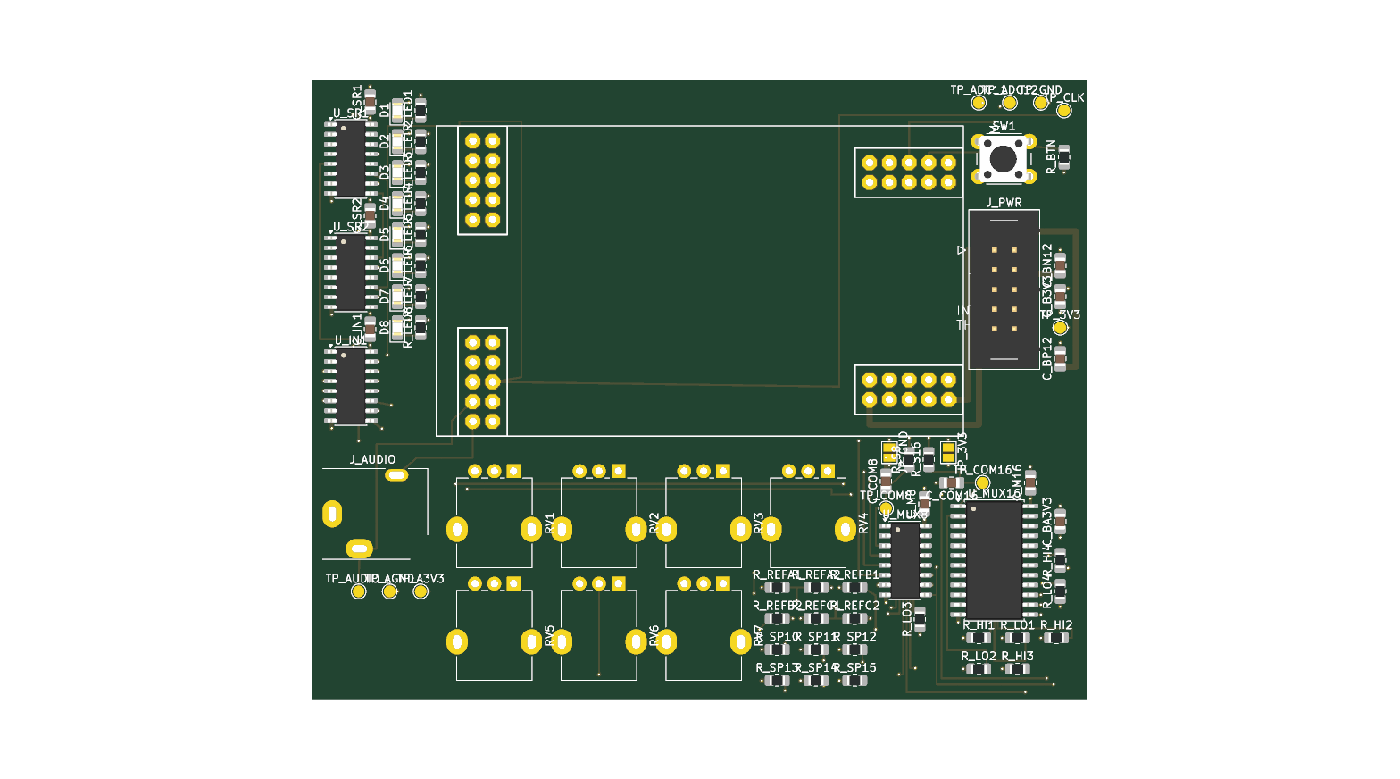
hardware/coupon/proof/coupon-board-front.png
