mcbronkowitch/fireflow/engine/mod/lane.cpp

#include "mod/lane.h"
#include "mod/waveforms.h"
#include "mod/range.h"
#include "util/math.h"
#include <cmath>

using namespace spky;

// Mutation character — tuned by ear; the spec fixes behavior, not constants.
static constexpr float kGravity  = 0.10f;  // GROW: mild pull toward 0 (the root)
static constexpr float kEndpointSampleEpsilon = 0.001f;

struct ProcessWindowEnd {
    double phase;
    int wraps;
};

// Rare endpoint fallback for tick(): replay only process()'s raw phase
// additions for the whole control window. Per-wrap rates come from the real
// tick traversal, so this shadow performs no events and consumes no RNG.
//
// This is a MODEL of process(), so its arithmetic must match process()'s
// exactly -- it moved from float to double together with _phase on 2026-08-12
// (PACE). If the two ever diverge again, tick()'s endpoint decision is made
// against a path the lane does not run, and the line "_phase =
// shadow_end.phase" below silently re-quantizes the accumulator.
static ProcessWindowEnd process_window_end(
    double phase, const double* phase_per_sample_by_wrap, int rate_count) {
    int wraps = 0;
    for (int sample = 0; sample < ModLane::kTickInterval; ++sample) {
        const int rate_index = wraps < rate_count ? wraps : rate_count - 1;
        phase += phase_per_sample_by_wrap[rate_index];
        while (phase >= 1.0) {
            phase -= 1.0;
            ++wraps;
        }
    }
    return {phase, wraps};
}

// x^n for an unsigned n by square-and-multiply: exact repeated squaring, so
// for kTickInterval = 96 it is x^64 * x^32 in seven multiplies. Used by
// _update_slew's tick twin in place of std::pow (see there).
static inline double pow_uint(double x, unsigned n) {
    double r = 1.0;
    while (n) {
        if (n & 1u) r *= x;
        x *= x;
        n >>= 1u;
    }
    return r;
}

// Positive modulo: _follow_offset can be negative after a backwards SPOT
// nudge, and C++'s % keeps the sign of the dividend.
static int slot_of(int32_t pos, int slots) {
    int m = static_cast<int>(pos % slots);
    if (m < 0) m += slots;
    return m;
}

void ModLane::init(float sample_rate, uint32_t seed) {
    _sr = sample_rate;
    _note_min_samples   = static_cast<int>(kFlowNoteMinS * _sr);
    _phrase_min_samples = kFlowPhraseSlots * _note_min_samples;
    _prime_floors();                        // primed: the first boundary fires
    _rng.seed(seed);
    _phase = 0.0;
#ifdef SPKY_TESTING
    _wraps = 0;   // re-init must zero the counter along with _phase, or a
                  // turns computation spanning a re-init reads a stale count
#endif
    _cur_step = -1;
    _stepped_out  = 0.f;
    _sh_prev_slot = -1;
    _shuffle_target = 0.f;
    _shuffle_latched = 0.f;
    if (_song.form_pending)
        _song.selected_form = _song.pending_form;
    if (_song.song_pending)
        _song.selected_song = _song.pending_song;
    _song.active_pattern = 0;
    _song.phrase_index = 0;
    MelodyPattern& pattern = _active_pattern();
    if (_melodic) {
        _generate_pattern_a();
        _derive_pattern_b();
        _song.active_pattern =
            song_symbol_at(_song.selected_song, _song.phrase_index);
    } else {
        _fill_walk();
        for (int i = 0; i < kSeqSlots; ++i) {
            pattern.gate[i] = true;
            pattern.motif_id[i] = 0;
        }
    }
    _melodic_at_init = _melodic;
    _song.form_pending = false;
    _song.song_pending = false;
    _song.new_pending = false;
    _song.length_pending = false;
    _density = 1.f;
    _target = 0.f;
    _fired = false;
    _wrapped = false;
    _frozen = false;
    _note_age = 0;
    _note_hold = 0;
    _ev_phase = 0.f;
    _ev_shape = 0.f;
    _ev_rate  = 0.f;
    _follow_pos    = 0;
    _follow_offset = 0;
    _follow_armed  = false;
    _follow_jumped = false;
    _shape_offset = 0.f;
    _kick_shape   = 0.f;
    _kick_coef    = std::exp(-1.f / (1.5f * _sr));   // SPOT shape decay tau = 1.5 s
    _settle_coef  = std::exp(-1.f / (0.3f * _sr));   // SETTLE glide tau = 0.3 s
    _kick_coef_tick   = std::pow(_kick_coef,   static_cast<float>(kTickInterval));
    _settle_coef_tick = std::pow(_settle_coef, static_cast<float>(kTickInterval));
    _settle_ctr   = 0;
    _update_slew();
    _slew.reset(0.f);
    _slew_tick.reset(0.f);
}

float ModLane::phase_eff() const {
    const double p = _phase + double(_ev_phase);
    return static_cast<float>(p - std::floor(p));
}

void ModLane::set_rate_hz(float hz)   { _rate_hz = hz > 0.f ? hz : 0.f; _update_inc(); }
void ModLane::set_shape(float s)      { _shape = clampf(s, 0.f, 1.f); }
void ModLane::set_range(float r)      { _range = clampf(r, 0.f, 1.f); }
void ModLane::set_variation(float v)  { _variation = clampf(v, -1.f, 1.f); }

void ModLane::set_form(Principle form) {
    int value = static_cast<int>(form);
    if (value < 0) value = 0;
    const int last = static_cast<int>(Principle::kCount) - 1;
    if (value > last) value = last;
    _song.pending_form = static_cast<Principle>(value);
    _song.form_pending = _song.pending_form != _song.selected_form;
}

void ModLane::set_song(SongMode song) {
    _song.pending_song = clamp_song(static_cast<int>(song));
    _song.song_pending = _song.pending_song != _song.selected_song;
}

void ModLane::set_flow_melody(bool on) {
    const bool mode_changed = on != _flow_melody;
    _flow_melody = on;
    // Only on a real flip, mirroring set_step's own `if (mode_changed)` line.
    // Part pushes this flag at BOTH sites that write _engine_id (part.cpp:43,
    // :441), so a same-class swap (SYNTH -> WAVE) calls this with the value it
    // already holds; re-priming the floors there would let a note fire sooner
    // than kFlowNoteMinS after the previous one, and clearing _cur_step there
    // would re-fire the slot the lane is already in.
    if (mode_changed) {
        // See set_step: a slot index and a freeze decision from the other
        // state mean nothing in this one. _cur_step = -1 makes the next sample
        // re-evaluate the boundary instead of holding whatever the FLOW LFO
        // path last wrote into _target -- the LFO writes _target every sample
        // but never moves _cur_step, so coming back to a still-matching index
        // fires nothing until the phase leaves the slot.
        //
        // Not while _step_mode is true: there the index is STEP's own live
        // position, and clearing it would re-fire the current step mid-step.
        // set_step clears it on its way out of STEP anyway.
        if (!_step_mode) _cur_step = -1;
        _frozen = false;
        _prime_floors();
    }
    // Absolute, not one-sided, and not conditional on the flip. ENTERING melody
    // mode the pattern may have been generated at another length -- at boot, or
    // whenever a host pushed a STEPS other than kFlowPhraseSlots before this
    // flag -- and pitch[] past that length is zero, so it MUST regenerate.
    // LEAVING it owes exactly the same flag: this call changes what
    // _effective_length() returns, and set_step's own length check is a DELTA
    // (old_len captured before its assignments) whose premise is that old_len
    // is the length the pattern was last generated at. An unflagged exit
    // destroys that premise, and STEP entered afterwards at an unchanged STEPS
    // then keeps the 8-slot melody groove -- see tests/test_flow_melody.cpp,
    // "leaving melody mode re-lengths the phrase for STEP". length_pending is
    // sticky and only consumed under _melody_engine_on(), so a lane that
    // leaves for the FLOW LFO path simply carries it until it enters a melody
    // mode again, which is the correct moment. Testing the pattern rather than
    // the flip gives every one of those cases from one condition.
    //
    // An ASSIGNMENT, not a one-sided raise -- and that is not tidiness, it is
    // the round trip. SYNTH -> SAMPLER -> SYNTH raises the flag on the way out
    // (8 != STEPS) and correctly declines to raise it on the way back (8 == 8),
    // but nothing on the LFO path consumes it, and the return leg's
    // `_cur_step = -1` above is precisely the condition _apply_preroll_work
    // waits for -- so a raise-only check rebuilds both patterns and restarts
    // the SONG ladder on the next sample, for a gesture that changed nothing.
    // The assignment clears it at the moment the two lengths agree again.
    //
    // Clearing here can never lose work another writer owes. The only other
    // raise is set_step's length delta, and the condition below is the ground
    // truth that delta approximates: pattern_groove.len IS the length the
    // phrase was last generated at (expand_pattern_groove writes it, and
    // derive_turnaround copies pattern A, so both patterns always carry the
    // same one), so when it equals _effective_length() there is no length work
    // left to do, whoever asked for it. The other pending flags are separate
    // fields and are untouched. The `_melodic` guard stays a guard rather than
    // folding into the assignment: a non-melodic lane can never raise this flag
    // (both raise sites test _melodic) and never consumes it either, so this
    // must not start writing one.
    if (_melodic)
        _song.length_pending =
            _active_pattern().pattern_groove.len != _effective_length();
    _update_slew();
}

void ModLane::set_step(bool on, int steps) {
    const bool entering_step = on && !_step_mode;
    const bool mode_changed  = on != _step_mode;
    if (entering_step) _shuffle_latched = _shuffle_target;
    if (entering_step) { _note_age = 0; _note_hold = 0; }  // STEP entry: no stale sustain
    // Either direction: a slot index and a freeze decision from the other mode
    // mean nothing in this one. _cur_step = -1 makes the first sample fire slot
    // 0, the same way init and reset do.
    if (mode_changed) { _cur_step = -1; _sh_prev_slot = -1; _frozen = false; _note_accent = 0.f; _prime_floors(); }
    // Entering STEP disarms the follower so its first follow() call lands on
    // the deck's current position instead of replaying the whole count.
    if (entering_step) { _follow_armed = false; _follow_jumped = false; }
    // Captured BEFORE the assignments below: _effective_length() reads
    // _step_mode and _steps, both of which this function is about to change.
    const int old_len = _melodic ? _effective_length() : 0;
    int new_steps = steps < 1 ? 1 : steps;
    if (on && _step_mode && new_steps != _steps && _cur_step >= 0) {
        // Seamless live STEPS turn (spec: step-clock): keep the step index and
        // the fraction inside it so the boundary grid never jumps; _cur_step
        // follows along so the next sample sees no ghost boundary. The
        // _cur_step >= 0 guard keeps pre-run configuration (init -> set_step
        // before the first process()) on the old path, where the first sample
        // must still fire step 0.
        // _cur_step is derived from the stored _phase (assigned first) using
        // the same warped lookup as process(), so a same-tick SPOT kick() +
        // STEPS turn is absorbed into this rescale (accepted trade).
        int old_step = shuffle_step_index(
            static_cast<float>(_phase), _steps, _shuffle_latched);
        float old_frac = shuffle_step_fraction(
            static_cast<float>(_phase), old_step, _steps, _shuffle_latched);
        float pos = std::fmod(
            static_cast<float>(old_step) + old_frac,
            static_cast<float>(new_steps));
        _phase = shuffle_phase_for_position(pos, new_steps, _shuffle_latched);
        _cur_step = shuffle_step_index(
            static_cast<float>(_phase), new_steps, _shuffle_latched);
    }
    _step_mode = on;
    _steps = new_steps;
    // Only when the EFFECTIVE length changes. Keep the _melodic guard: the
    // helper clamps to kSeqSlots, and lane_slots() can hand a texture lane up
    // to 64 (tests/test_lane_len.cpp:26), so an unguarded check would start
    // clamping lengths that today pass through.
    if (_melodic && _effective_length() != old_len)
        _song.length_pending = true;
    if (entering_step && _melodic_at_init &&
        _song.patterns[1].pattern_groove.len == 0)
        _song.new_pending = true;
    _update_inc();
}

// Spec 2026-07-17 step-clock: STEP runs RATE as a step clock with an 8-step
// reference; FLOW keeps RATE as the cycle rate. At 8 steps the factor is
// exactly 1.0f, so the panel default stays bit-identical to the old
// pattern-clock behavior.
void ModLane::_update_inc() {
    _phase_inc = (double(_rate_hz) / double(_sr)) * double(clock_scale());
    _update_slew();     // SMOOTH's tau is a fraction of the interval this sets
}

void ModLane::new_phrase() {
    if (_melodic) _song.new_pending = true;
}

int ModLane::_effective_length() const {
    if (_flow_melody_on()) return kFlowPhraseSlots;
    int n = _steps < 1 ? 1 : _steps;
    return n > kSeqSlots ? kSeqSlots : n;
}

void ModLane::_generate_pattern_a() {
    MelodyPattern& pattern = _song.patterns[0];
    const int len = _effective_length();
    generate_phrase(_song.selected_form, _rng, len,
                    pattern.pitch, pattern.gate, pattern.motif_id,
                    pattern.layout);
    pg_gen_groove(_rng, pattern.layout.motif_len, pattern.cell_groove);
    expand_pattern_groove(
        pattern.cell_groove, len, pattern.pattern_groove);
}

void ModLane::_derive_pattern_b() {
    derive_turnaround(_song.patterns[0], _effective_length(), _rng,
                      _song.patterns[1],
                      _song.cadence_slot, _song.bound_a_opening);
}

void ModLane::_clear_fresh_phrase_state() {
    _note_age = 0;
    _note_hold = 0;
    _ev_phase = 0.f;
    _ev_shape = 0.f;
    _ev_rate = 0.f;
}

void ModLane::_apply_pending_song_work() {
    const bool rebuild =
        _song.form_pending || _song.new_pending ||
        _song.length_pending ||
        _song.patterns[1].pattern_groove.len == 0;

    if (_song.form_pending)
        _song.selected_form = _song.pending_form;
    if (_song.song_pending)
        _song.selected_song = _song.pending_song;

    if (rebuild) {
        _generate_pattern_a();
        _derive_pattern_b();
        _clear_fresh_phrase_state();
    }

    _song.phrase_index = 0;
    _song.active_pattern =
        song_symbol_at(_song.selected_song, _song.phrase_index);
    if (_song.active_pattern == 1u)
        bind_song_cadence(
            _song.patterns[0], _song.patterns[1],
            _song.cadence_slot, _song.bound_a_opening);

    _song.form_pending = false;
    _song.song_pending = false;
    _song.new_pending = false;
    _song.length_pending = false;
}

void ModLane::_apply_preroll_work() {
    if (_melody_engine_on() && _cur_step < 0 &&
        (_song.form_pending || _song.song_pending ||
         _song.new_pending || _song.length_pending))
        _apply_pending_song_work();
}

void ModLane::_advance_song() {
    ++_song.phrase_index;
    const uint8_t incoming =
        song_symbol_at(_song.selected_song, _song.phrase_index);
    if (incoming == 1u) {
        bind_song_cadence(
            _song.patterns[0], _song.patterns[1],
            _song.cadence_slot, _song.bound_a_opening);
    }
    _song.active_pattern = incoming;
}

void ModLane::set_smooth(float s) {
    const float c = clampf(s, 0.f, 1.f);
    // Hosts push every knob on every control tick. _update_slew's other
    // inputs each recompute on their own change, so an unchanged SMOOTH
    // only owes the _ev_rate refresh (refresh_slew, lane.h).
    if (_skip_unchanged && same_bits(c, _smooth)) { refresh_slew(); return; }
    _smooth = c;
    _update_slew();
}

void ModLane::refresh_slew() {
    if (!same_bits(_ev_rate, _slew_ev_rate)) _update_slew();
}

void ModLane::set_fixed_slew(bool on) {
    _fixed_slew = on;
    _update_slew();
}

void ModLane::_update_slew() {
#ifdef SPKY_TESTING
    ++_slew_updates;
#endif
    _slew_ev_rate = _ev_rate;   // what refresh_slew() compares against
    // SMOOTH is a fraction of the lane's own INTERVAL, not a wall-clock time.
    // The old law was `0.00002 * pow(25000, _smooth)` -- absolute seconds
    // against cycles spanning four decades, so the knob's reach was whatever
    // the rate made it: inert on a 40 s cycle, annihilating on a 0.03 s one.
    // Spec: docs/superpowers/specs/2026-08-13-shape-smooth-rework-design.md 1-2.
    //
    // _fixed_slew keeps the absolute 0.02 s on purpose. It is reachable only
    // from the render host's set_fixed_slew scenario action and is an
    // absolute-seconds escape hatch for test fixtures (spec 4).
    float t;
    if (_fixed_slew) {
        t = 0.02f;
    } else {
        // Samples per cycle. _ev_rate is part of the phase advance, exactly as
        // in step_samples(). It is deliberately NOT a recompute trigger: it
        // decays every tick while _settle_ctr runs (tick(), :871), so treating
        // it as one would rebuild both slews on every sample of every settle.
        // tau is therefore computed from the _ev_rate standing at the last
        // real parameter change, which is the resting value the lane returns
        // to anyway -- or, on a host that pushes every knob every control
        // tick, at the last push: the unchanged-value early-outs keep that
        // per-push refresh through refresh_slew() (lane.h).
        const double denom = _phase_inc * (1.0 + double(_ev_rate));
        double interval = 0.0;                 // in SAMPLES
        if (denom > 0.0) {
            const double cycle = 1.0 / denom;
            if (_step_mode) {
                // One STEP of THIS lane. Note the slot count CANCELS: in STEP
                // clock_scale() is 8/_steps, so cycle/_steps is
                // sr/(8*rate*(1+_ev_rate)) whatever _steps is. Measured at
                // master 0.5 Hz, deck steps 8: SOURCE/SIZE/MOTION/LEVEL carry
                // slot counts 4/16/12/6 and all four land on tau = 4284.00
                // samples exactly. What differs per lane is tau/CYCLE, because
                // cycle = step * slots does differ -- which is what spec 2.3's
                // attenuation table shows (monotone in slots). Spec 2.3's prose
                // explains it as "a different tau per lane"; that mechanism is
                // wrong, its numbers are not. Corrected 2026-08-15.
                interval = cycle / double(_steps);
            } else if (_flow_melody_on()) {
                // One SLOT, floored at the note minimum: where the floor
                // decimates, the raw slot is far shorter than the notes
                // actually are, and using it would glide much tighter than
                // anything needs.
                const double slot = cycle / double(_effective_length());
                const double floor_s = double(_note_min_samples);
                interval = slot > floor_s ? slot : floor_s;
            } else {
                // FLOW LFO: the lane cycle. NOTE _effective_length() is wrong
                // here -- it returns _steps on this path, not 1.
                interval = cycle;
            }
        }
        const float top = _melodic ? kFlowSlewFrac : kSmoothTopTexture;
        t = static_cast<float>(double(_smooth) * double(top) * interval)
          / _sr;
        // OnePole::init treats time_s <= 0 as passthrough (k = 1), which is the
        // right behaviour at SMOOTH 0 -- but floor it at one sample so a
        // stopped lane (denom == 0) cannot produce a negative or NaN tau.
        const float min_t = 1.f / _sr;
        if (!(t > min_t)) t = min_t;
    }
    _slew.init(_sr, t);
    // Tick twin: the exact kTickInterval-sample compound of the per-sample
    // coefficient, so held segments converge identically at tick sampling.
    // The `k` derivation + clamp below intentionally mirrors OnePole::init's
    // own coefficient formula (engine/util/onepole.h) so that compounding it
    // kTickInterval times reproduces the per-sample coefficient's effect
    // exactly. If that formula changes, this must change with it -- these
    // two are a matched pair, not independent code, and this tick twin would
    // otherwise silently diverge from process()'s slew.
    // In DOUBLE, and not as a style preference. Under the old absolute law tau
    // was capped at 0.5 s, so k never fell below 4e-5. It is now proportional
    // to the cycle, and at the slow end of the panel k reaches ~1e-8. In float
    // `1.f - k` rounds to exactly 1.0f below half an ulp (k < 2.98e-8), so the
    // power is 1 and the coefficient QUANTISES -- and at the extreme reaches
    // exactly zero, which is a one-pole that never moves again.
    //
    // Measured on ModLane driven directly at 0.0003125 Hz (what RATE 0 + PACE 0
    // hand LANE_SIZE), 60 s: p2p 0.000000000 at SMOOTH 0.50, 0.70 and 1.00, and
    // one single coefficient shared by every knob position from 0.15 to 0.40.
    // Through the whole instrument the outright freeze is NOT reachable -- other
    // per-tick motion keeps p2p off zero -- but the quantisation is, and
    // tests/test_smooth_law.cpp's G6 gates it there.
    //
    // The per-sample _slew above is NOT affected: k itself is perfectly
    // representable, and it was measured tracking the analytic settling curve
    // at these same tau values. Only this half of the pair needs the precision.
    //
    // The power is an integer one, by repeated squaring (pow_uint, above) and
    // not std::pow: the firmware build calls the latter as newlib's software
    // double pow, once per slew rebuild (2026-10-09). Still in double. Against
    // std::pow over k in [1e-9, 1] the stored float coefficient differs by at
    // most 1 ulp, in 0.47 % of points (relative error of 1 - x^96 <= 1.05e-8
    // down to k = 1e-10).
    double k = 1.0 / (double(t) * double(_sr));
    if (k > 1.0) k = 1.0;
    _slew_tick.set_coef(static_cast<float>(
        1.0 - pow_uint(1.0 - k, static_cast<unsigned>(kTickInterval))));
}

void ModLane::kick(float dphase, float dshape) {
    _phase += double(dphase);
    _phase -= std::floor(_phase);          // permanent wrap into [0,1)
    _kick_shape += dshape;                 // decays back to 0 over ~1.5 s
}

void ModLane::nudge_slots(int n, float dshape) {
    // Move the offset AND the remembered position by the same amount: the
    // jump must not look like elapsed time, or the next follow() would replay
    // n slots (or, for a negative n, stall until the deck caught back up).
    _follow_offset += n;
    _follow_pos    += n;
    // A draw that rounds to n == 0 lands on the same slot it already occupies
    // -- there is no new slot to make audible, so no forced re-entry at the
    // next follow(). Same call FLOW makes for a near-zero dphase in kick():
    // the shape kick still applies unconditionally (it is real at any draw),
    // but nothing else moves.
    if (n != 0) _follow_jumped = true;
    _kick_shape += dshape;
}

float ModLane::follow(int32_t deck_step, float frac, float shuffle) {
    _fired   = false;
    _wrapped = false;
    _apply_preroll_work();
    _kick_shape *= _kick_coef_tick;
    if (_settle_ctr > 0) {
        _settle_ctr = _settle_ctr > kTickInterval ? _settle_ctr - kTickInterval : 0;
        _ev_phase   *= _settle_coef_tick;
        _ev_shape   *= _settle_coef_tick;
        _ev_rate    *= _settle_coef_tick;
        _kick_shape *= _settle_coef_tick;
    }

    const int     slots = _steps < 1 ? 1 : _steps;
    const int32_t pos   = deck_step + _follow_offset;
    const int     here  = slot_of(pos, slots);

    bool    land_only = false;
    int32_t elapsed   = 0;
    if (!_follow_armed) {
        // First call after init/reset/STEP entry. Land on the current position
        // without replaying every step the deck has taken since it started --
        // and, just as important, WITHOUT running a wrap even when the landing
        // slot is 0. Wrap events evolve the pattern that just ENDED
        // (_evolve_outgoing_pattern); at a cold start none did. STEP entry
        // restarts the deck count at 0, so treating that as a wrap would walk
        // EVOLVE once on all four texture lanes every time the switch is
        // thrown. tick() makes the same choice at its own cold start: it
        // enters the step its phase points at and runs no wrap events.
        _follow_armed = true;
        land_only     = true;
    } else {
        elapsed = pos - _follow_pos;
        if (elapsed < 0) elapsed = 0;          // only nudge_slots moves backwards
        // A jump this large means the caller skipped a long stretch (a stopped
        // transport, a mode switch). Replaying it would burn RNG draws for
        // cycles nobody heard; land on the current slot instead. Same spirit
        // as tick()'s edge-walk guard.
        if (elapsed > 2 * kSeqSlots) land_only = true;
    }

    bool entered = false;
    if (land_only) {
        _phase = shuffle_phase_for_position(
            static_cast<float>(here), slots, shuffle);
        _enter_step(here);
        entered = true;
    } else {
        const int32_t prev = pos - elapsed;
        for (int32_t k = 1; k <= elapsed; ++k) {
            const int slot = slot_of(prev + k, slots);
            // Boundary targets are evaluated at the exact grid phase, the same
            // sampling tick() documents for its edge walk.
            _phase = shuffle_phase_for_position(
                static_cast<float>(slot), slots, shuffle);
            if (slot == 0) {
                _wrapped = true;
                _wrap_events();      // before the new cycle's step 0, as in tick()
            }
            _enter_step(slot);
            entered = true;
        }
    }
    _follow_pos = pos;

    if (_follow_jumped) {
        _follow_jumped = false;
        if (!entered) {
            _phase = shuffle_phase_for_position(
                static_cast<float>(here), slots, shuffle);
            _enter_step(here);
        }
    }

    // Park at the live position so phase(), phase_eff() and any external
    // reader see where the lane actually is inside its slot.
    _phase = shuffle_phase_for_position(
        static_cast<float>(here) + frac, slots, shuffle);

    const float out = apply_range(_slew_tick.process(_target), _range);
    _latch_stepped(out);
#ifdef SPKY_TESTING
    _last_out = out;
#endif
    return out;
}

void ModLane::settle() {
    _settle_ctr = static_cast<int>(_sr * 1.0f);   // glide EVOLVE + kick over ~1 s
}

void ModLane::reset(float phase) {
    _phase = clampf(phase, 0.f, 0.999999f);
    _shuffle_latched = _shuffle_target;
    _cur_step = -1;
    _sh_prev_slot = -1;
    // Until 2026-08-13 (Task 11, FLOW melody engine plan) this line was
    // observable through tick() only: process() re-evaluates the boundary on
    // its very next call regardless (_cur_step == -1 forces slot 0, always
    // open, so _on_boundary recomputes _frozen to false on its own), but
    // tick()'s FLOW-melody path had no such immediate re-check, so a freeze
    // could survive RST into the next tick() call with nothing to clear it.
    // Task 11 gave tick() the same immediate pending-mismatch re-check
    // process() already had (both paths now force-evaluate slot 0 on their
    // very next call after reset()), so this line is superseded by BOTH
    // paths' next call the same way and no longer has a downstream-behavior
    // consequence through either one. It is still observable directly,
    // though: nothing else in reset() touches _frozen, so querying
    // frozen() between reset() and the next process()/tick() call reads
    // this line and only this line. See tests/test_flow_melody.cpp, "RST
    // clears a stale freeze immediately, before the next process()/tick()
    // call" (re-homed there by Task 11 when the original tick()-path case
    // stopped being able to fail -- see that task's report for the
    // measurement).
    _frozen = false;
    // RST is the resync gesture: it clears the SPOT offset too, so the lane
    // comes back to the deck's own slot 0 rather than to a stumbled one.
    _follow_pos    = 0;
    _follow_offset = 0;
    _follow_armed  = false;
    _follow_jumped = false;
    _note_age = 0;
    _note_hold = 0;
    _prime_floors();
    _slew.reset(_target);
    _slew_tick.reset(_target);
}
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
